OpenSkyHawk/OpenSkyhawk/docs/hardware/cad-workflow.md

---
status: stub
---

# CAD Workflow

!!! warning "Work in Progress"
    This page is being written. Check back soon or
    [contribute to the docs](../contributing/index.md).

!!! note "CAD Tooling Under Evaluation"
    CAD tooling is currently being evaluated between Fusion 360 and FreeCAD.
    FreeCAD is the preferred direction for alignment with the open source nature
    of the project. This page will be updated once a tool is selected.
    The file management policy (source files committed, STL/STEP exports
    gitignored and published via GitHub Releases) applies regardless of tool choice.
