OpenSkyHawk/OpenSkyhawk/Firmware/ScratchPad/TechSpec/STM32Board.md

# STM32Board — Technical Specification

**Status:** Done

**FirmwarePlan ref:** `FirmwarePlan/08-hardware-firmware-contracts.md#status-led--bi-color-redgreen`,
`FirmwarePlan/08-hardware-firmware-contracts.md#diagserial--usart1`,
`FirmwarePlan/02-can-protocol.md#can-bus-configuration`,
`FirmwarePlan/09-startup-resync-diagnostics.md`

**Depends on:** `CANProtocol.md` (for the `CanStatus` event type)

---

## Responsibility

Initialises and manages all shared hardware present on every STM32 board: SWD-only debug (JTAG
released at boot, #299), bi-color status LED (PB14/PB15), DiagSerial (USART1/Serial1), and CAN
peripheral hardware configuration. Exposes
`NODE_ID` (compile-time constant from build_flags) with range validation at compile time.
Owns the LED state machine and tick-based animation driver.

Reacts to CAN bus status events via `onCanStatus()` — it does not poll CANProtocol and is
not directly controlled by the sketch or by CANProtocol. `CanStatus` is owned by
CANProtocol; STM32Board only translates those events into its private LED state machine.

Does **not** start the CAN peripheral or configure receive filters — that belongs to
`CANProtocol::start()`. Does not own any panel-specific I/O.

---

## File Layout

```
Firmware/Libraries/STM32Board/
├── STM32Board.h
├── STM32Board.cpp
└── library.json
```

Included in every STM32 sketch:
```cpp
#include <STM32Board.h>
```

Implemented as a `namespace` — there is always exactly one STM32 board per firmware build,
so a class with instances would be a fiction. Internal state variables are defined in
`STM32Board.cpp` only (not exposed in the header), keeping the public API clean.

### Test project

```
Firmware/Tests/STM32Board/
├── platformio.ini                 — 3 visual envs + 4 STM32BOARD_TEST assertion envs
│                                    + 2 ADC-prescaler envs
└── tests/
    ├── led_state_machine/
    │   └── led_state_machine.cpp   — visual: cycles all 7 LedStates (onCanStatus 4 + setLinkActive
    │                                 CONNECTED + setWarning WARNING); OFF shown pre-begin()
    ├── diag_serial/
    │   └── diag_serial.cpp         — setDebug(false): log() produces no output; setDebug(true):
    │                                 log() emits the expected string on Serial1 at 115200 baud
    ├── can_status_wiring/
    │   └── can_status_wiring.cpp   — calls onCanStatus() with each CanStatus value; verifies
    │                                 the correct LedState is entered (checks pin behaviour via tick())
    ├── state_precedence/           — [STM32BOARD_TEST] currentState() asserts the precedence table:
    │                                 CONNECTED engage/suppress/re-engage, WARNING vs CAN faults
    ├── link_decay/                 — [STM32BOARD_TEST] CONNECTED → NORMAL after LINK_DECAY_MS;
    │                                 refresh holds it
    ├── warning_clear/              — [STM32BOARD_TEST] setWarning(true/false) latch; no-arg raises
    ├── animation_timing/           — [STM32BOARD_TEST] CONNECTED solid (no toggle) vs NORMAL blink,
    │                                 via direct PB14/PB15 pin reads
    ├── jtag_release/
    │   └── jtag_release.cpp        — PA15/PB4 as input + pull-down via HAL_GPIO_Init (not pinMode,
    │                                 which releases them itself): read 1 before begin() (JTAG's
    │                                 pull-up wins), 0 after (GPIO owns them). #299
    └── adc_clock/
        └── adc_clock.cpp           — asserts ADCPRE == /6 and ADCCLK inside the F103 window (#263).
                                      Built into TWO envs: test_adc_clock (72 MHz path) and
                                      test_adc_clock_fallback (-DFORCE_CLOCK_FALLBACK, 8 MHz path)
                                      — the pair is what proves both SystemClock_Config exit paths
                                      set it. Also prints liveTemp/liveVdd for before/after.
```

The four `STM32BOARD_TEST` envs, the two `adc_clock` envs and `jtag_release` print `PASS`/`FAIL` per assertion plus
an `ALL PASS` summary over DiagSerial; the three visual envs are observed against the animation map.

> **Status-LED convention in this suite.** No sketch here calls `CANProtocol::start()` — they test
> `STM32Board` in isolation — so `_canStatus` never leaves its initial `CanStatus::STARTING` and
> `_recompute()` parks in **`BOOTING` (red 1 s blink) for the whole run**. That resting state is
> indistinguishable from a node that failed to bring CAN up, and it says nothing about whether the
> assertions passed.
>
> `adc_clock` therefore drives the LED from its **result**: pass → `onCanStatus(CanStatus::NORMAL)`
> → **green 1 Hz**, the healthy-node pattern; fail → `setWarning(true)` → red/green alternating. A
> **red 1 s blink means `setup()` never reached the end.** `onCanStatus()` is a result indicator
> here, not a claim about the bus (`led_state_machine` drives it artificially too, and neither
> sketch starts CAN). In `test_adc_clock_fallback` the faked dead crystal latches `_clockFault`,
> which outranks both, so that env always shows WARNING — read it by DiagSerial.
>
> Separately, halting the core under SWD (`dump_image`, `mdw`, a paused upload) freezes the GPIOs
> mid-blink; caught on an LED-on phase it sits **solid**, resembling `BUS_OFF` (solid red) or
> `CONNECTED` (solid green) when the CPU is merely stopped.

`adc_clock` asserts the `ADCPRE` bits in both envs — those are what the change writes, and they are
exact. The frequency is pinned to a literal only on the 72 MHz path, where `72e6 / 6 = 12000000`
exactly; the fallback's `8e6 / 6` truncates to 1333333, so there it is printed and range-checked
against the 0.6–14 MHz window instead of hard-coded.

`can_status_wiring.cpp` verifies the mapping from CANProtocol's `CanStatus` values to
STM32Board's private LED states, so both libraries must be in `lib_deps`:

```ini
[platformio]
src_dir = tests

[env_base]
platform = ststm32@^20.0.0
board = genericSTM32F103C8
framework = arduino
build_flags =
    -DNODE_ID=1
    -DHAL_CAN_MODULE_ENABLED
    -DUSB_NONE
    -DHSE_VALUE=8000000
lib_extra_dirs = ${PROJECT_DIR}/../../Libraries
lib_deps =
    STM32Board
    CANProtocol

[env:test_led_state_machine]
extends = env_base
build_src_filter = -<*> +<led_state_machine/led_state_machine.cpp>

[env:test_diag_serial]
extends = env_base
build_src_filter = -<*> +<diag_serial/diag_serial.cpp>

[env:test_can_status_wiring]
extends = env_base
build_src_filter = -<*> +<can_status_wiring/can_status_wiring.cpp>

; Same source, two envs — the second forces the SystemClock_Config fault path (#263)
[env:test_adc_clock]
extends = env_base
build_src_filter = -<*> +<adc_clock/adc_clock.cpp>

[env:test_adc_clock_fallback]
extends = env_base
build_flags = ${env_base.build_flags} -DFORCE_CLOCK_FALLBACK
build_src_filter = -<*> +<adc_clock/adc_clock.cpp>
```

CAN bus integration testing is out of scope here — see CANProtocol TechSpec.

---

## Public API

```cpp
// STM32Board.h

enum class CanStatus;

namespace STM32Board {

    /**
     * @brief Initialise all shared hardware. Call once at the top of setup().
     *
     * Releases JTAG and keeps SWD (#299), so PA15 / PB3 / PB4 are ordinary GPIO from here on.
     * Configures PB14 (Red) and PB15 (Green) as outputs and enters BOOTING state.
     * Starts DiagSerial (USART1, PA9/PA10, 115200 baud) — silent until setDebug(true).
     * Calls analogReadResolution(16) — framework scales 12-bit ADC output to 16-bit range
     * (0–65520) for all subsequent analogRead() calls; PinRef::readAnalog() relies on this.
     * The ADC clock itself is set earlier, in SystemClock_Config (ADCPRE /6 → 12 MHz, #263) —
     * begin() only reads it back for the diag line.
     * Configures the CAN peripheral at 500 kbps on PA11/PA12 but does NOT start it —
     * call CANProtocol::start() after filter setup.
     * NODE_ID range (0–63) is validated at compile time via static_assert.
     */
    void begin();

    /**
     * @brief Enable or disable DiagSerial output.
     *
     * DiagSerial is always initialised by begin(); this flag gates all log() calls.
     *
     * @param on True to emit output on USART1; false for silence (default).
     */
    void setDebug(bool on);

    /**
     * @brief Drive LED animations. Call once per loop() iteration.
     *
     * Advances blink state using millis(). Fully non-blocking — no busy-wait or delay.
     */
    void tick();

    /**
     * @brief CAN bus status event handler.
     *
     * Called when CANProtocol fires a status change.
     * Maps CanStatus to an internal LedState — the sketch and CANProtocol never
     * access the LED directly.
     *
     * @param status New CAN bus status reported by CANProtocol.
     * @note CanStatus is defined by CANProtocol.h and forward-declared here to keep
     *       STM32Board.h light. STM32Board.cpp includes CANProtocol.h for the enum values.
     */
    void onCanStatus(CanStatus status);

    /**
     * @brief Raise or clear the WARNING condition — red/green alternating at 500 ms.
     *
     * Call for any non-CAN fault: dead PanelGroup node (PanelBridge), lost master
     * heartbeat (PanelGroup), SYNC timeout, I²C bus hang. CanStatus has no WARNING value —
     * this is the only public entry point for that state. WARNING is a clearable latch:
     * call setWarning(false) once the condition recovers. It outranks CONNECTED/NORMAL but
     * is masked by any CAN fault (CAN_ERROR/BUS_OFF).
     *
     * @param on True to raise WARNING (default); false to clear it.
     */
    void setWarning(bool on = true);

    /**
     * @brief Signal that application data is flowing → CONNECTED (green solid).
     *
     * Call setLinkActive(true) on each unit of inbound data (PanelBridge: a DCS-BIOS export
     * seen; PanelGroup: a CTRL_BCAST received). The link auto-decays back to NORMAL after
     * ~500 ms (LINK_DECAY_MS) with no further calls, evaluated inside tick(). CONNECTED is
     * shown only while the CAN bus is healthy; a CAN fault masks it and it re-engages
     * automatically on recovery if data is still flowing.
     *
     * @param active True to (re)assert the data-flowing link; false to drop it immediately.
     */
    void setLinkActive(bool active);

    /**
     * @brief Returns true when debug output is enabled.
     *
     * Guard multi-field formatted print blocks with this to avoid string formatting
     * overhead when debug is off.
     */
    bool isDebug();

    /**
     * @brief Print a line to DiagSerial if debug is enabled; no-op otherwise.
     * @param msg Null-terminated string to print.
     */
    void log(const char* msg);

    /**
     * @brief Access DiagSerial directly for multi-field formatted output.
     *
     * Guard with isDebug() to avoid formatting overhead when debug is off.
     *
     * @returns Reference to the USART1 Uart instance.
     */
    Uart& diagSerial();

    /**
     * @brief Read the MCU internal die temperature (ADC ch16) as whole °C (#213).
     *
     * Reads ATEMP + AVREF (Vrefint) and converts with F103 datasheet typicals
     * (V25 = 1.43 V, Avg_Slope = 4.3 mV/°C), referencing Vsense to the measured Vdd.
     * UNCALIBRATED — ~±few °C absolute, die (not ambient), self-heat offset.
     *
     * @returns Die temperature in whole °C, or INT8_MIN if internal channels are unavailable.
     */
    int8_t readDieTempC();

    /**
     * @brief Estimate MCU Vdd from Vrefint (ADC ch17), in millivolts (#213).
     *
     * @note Uses the F103 typical Vrefint of 1.20 V (no VREFINT_CAL on F103).
     * @returns Vdd in millivolts, or 0 if the internal reference is unavailable.
     */
    uint16_t readVddMv();

    /**
     * @brief Edge-log a node's aggregated fault transition to DiagSerial (#163).
     *
     * Prints `[<tag>] degraded: <detail> (fault N)` / `[<tag>] recovered` on a change only,
     * isDebug()-gated. Shared by every node's health-TX loop (PanelGroup "NODE", PanelBridge
     * "BRIDGE", future PDU) — one static prev-fault, correct because a binary has ONE node
     * identity. Detail strings stay local (never on the CAN wire).
     */
    void logNodeFaultEdge(const char* tag, NodeFaultCode fault, const char* detail);

    static constexpr uint8_t PIN_LED_RED   = PB14;  ///< Red LED pin — same on all STM32 boards
    static constexpr uint8_t PIN_LED_GREEN = PB15;  ///< Green LED pin — same on all STM32 boards

} // namespace STM32Board
```

NODE_ID compile-time validation, placed at file scope in `STM32Board.h`:
```cpp
static_assert(NODE_ID <= 63,
    "NODE_ID must be 0–63. 0 = PanelBridge (reserved); 1–63 = PanelGroup nodes.");
```

### Sketch wiring

The sketch is the integration point:

```cpp
// setup()
STM32Board::begin();
CANProtocol::onStatusChange(STM32Board::onCanStatus);
CANProtocol::start();

// loop()
STM32Board::tick();
```

`CANProtocol::onStatusChange()` is defined in the CANProtocol TechSpec.

---

## Key Data Structures

### LedState (private enum)

```cpp
enum class LedState {
    OFF,        // both LEDs off — pre-begin() only
    BOOTING,    // red slow blink  (1000 ms) — initialising
    NORMAL,     // green slow blink (1000 ms) — CAN healthy, no data flowing
    CONNECTED,  // green solid                — CAN healthy and data flowing
    CAN_ERROR,  // red fast blink  (250 ms)  — TEC > 0, errors accumulating
    BUS_OFF,    // red solid                  — CAN controller halted
    WARNING     // red/green alternating (500 ms) — app-layer degraded state
};
```

`LedState` is an internal type — not exposed in the public API. The on-target tests need to
assert it, so the `STM32BOARD_TEST` macro (set only by the test envs) moves the enum to the
header and exposes a read-only `LedState currentState()` accessor; production builds keep both
private.

### LedState → Animation Map

| State | Red | Green | Blink period |
|---|-----|---|---|
| `OFF` | off | off | — |
| `BOOTING` | blink | off | 1000 ms |
| `NORMAL` | off | blink | 1000 ms |
| `CONNECTED` | off | solid on | — |
| `CAN_ERROR` | blink | off | 250 ms |
| `BUS_OFF` | solid on | off | — |
| `WARNING` | alternating | alternating | 500 ms |

For `WARNING`: phase 0 → red on, green off; phase 1 → red off, green on.

### State arbitration & precedence

The LED state is **derived**, not set last-writer-wins. `STM32Board` stores three independent
inputs — the last `CanStatus`, a data-flowing link flag (with timestamp, set by
`setLinkActive`), and a warning latch (`setWarning`) — and a single internal `_recompute()`
picks the effective `LedState` by fixed precedence (highest first):

| Priority | Condition | LedState |
|---|---|---|
| 1 | not begun | `OFF` |
| 2 | `CanStatus::BUS_OFF` | `BUS_OFF` |
| 3 | `CanStatus::TX_ERROR` | `CAN_ERROR` |
| 4 | `CanStatus::STARTING` | `BOOTING` |
| 5 | warning latched | `WARNING` |
| 6 | `CanStatus::NORMAL` **and** link active | `CONNECTED` |
| 7 | `CanStatus::NORMAL` | `NORMAL` |

CAN-health faults outrank the app-layer WARNING (a dead/erroring bus must never be masked).
WARNING outranks CONNECTED/NORMAL. CONNECTED is guarded on `NORMAL`, so a CAN fault
auto-suppresses it and it re-engages on recovery if the link has not yet decayed
(`LINK_DECAY_MS` = 500 ms). `_recompute()` resets the blink phase and repaints only on an
actual state change.

### CanStatus → LedState mapping

`onCanStatus()` stores the `CanStatus` and calls `_recompute()`; rows 2–4, 6–7 above are the
effective mapping (CONNECTED/NORMAL both correspond to `CanStatus::NORMAL`, differentiated by
the link flag):

| CanStatus | LedState (no link) | LedState (link active) |
|---|---|---|
| `STARTING` | `BOOTING` | `BOOTING` |
| `NORMAL` | `NORMAL` | `CONNECTED` |
| `TX_ERROR` | `CAN_ERROR` | `CAN_ERROR` |
| `BUS_OFF` | `BUS_OFF` | `BUS_OFF` |

`CanStatus` is defined in `CANProtocol.h`. See CANProtocol TechSpec for the full enum.

> **ERROR_PASSIVE (EPVF / TEC ≥ 128)** is intentionally **not** a distinct LED state — it stays
> folded into `CAN_ERROR`, and EPVF remains visible via the heartbeat `flags` byte. See
> `FirmwarePlan/11-open-issues.md` (re-confirmed in #93).

---

## Implementation Notes

### tick() — blink state machine

```cpp
void STM32Board::tick() {
    uint32_t now = millis();

    // Decay the data-flowing link → CONNECTED falls back to NORMAL after a quiet gap.
    if (_linkActive && (now - _linkLastMs) >= LINK_DECAY_MS) {
        _linkActive = false;
        _recompute();
    }

    uint16_t period = _blinkPeriodFor(_state);  // 0 = solid or off
    if (period > 0 && (now - _ledLastToggleMs) >= (uint32_t)(period / 2)) {
        _blinkPhase      = !_blinkPhase;
        _ledLastToggleMs = now;
        _applyLed();  // only called when phase actually changes
    }
    // solid/off states: pins already set by _recompute() — nothing to do here
}
```

`_applyLed()` is called in two places only:
- Inside `_recompute()` — applies the new state immediately on a transition (and only then)
- Inside `tick()` — only when `_blinkPhase` toggles

`_recompute()` is the **sole writer** of `_state`: `onCanStatus()`, `setWarning()`,
`setLinkActive()`, and the `tick()` decay path all update one input field and call it.

`digitalWrite()` is called exactly twice per blink cycle for blinking states, and once per
state transition for solid and off states. Pins are never written redundantly.

### NODE_ID — PanelBridge reservation

`NODE_ID=0` is reserved for PanelBridge. PanelBridge is a STM32 board and a valid CAN bus
participant, but it is the master node — it does not have a sub-node address in the
0x101–0x43F frame ID ranges used by PanelGroup nodes.

The `static_assert` uses `<= 63` (no lower bound) so PanelBridge passes with `NODE_ID=0`:

```cpp
static_assert(NODE_ID <= 63,
    "NODE_ID must be 0–63. 0 is reserved for PanelBridge; 1–63 for PanelGroup nodes.");
```

SimGateway is an RP2040 — it does not use STM32Board and has no NODE_ID concern.

### CAN peripheral configuration

`begin()` configures the STM32 CAN peripheral (baud rate prescaler, segment timing for
500 kbps, PA11/PA12 alternate function) but does **not** call the HAL start function.
The peripheral is left configured-but-stopped — ready for `CANProtocol::start()`.

**Library choice:** direct STM32duino HAL (`CAN_HandleTypeDef`, `HAL_CAN_Init`) — no
wrapper library. Confirmed by the prototype CAN stress test (Experiment B).

**Clock tree:** 8 MHz crystal × PLL ×9 = 72 MHz SYSCLK; APB1 prescaler /2 = **36 MHz APB1**
(STM32F103 APB1 max is 36 MHz; CAN1 is on APB1); APB2 prescaler /1 = **72 MHz APB2**, from which
`ADCPRE` /6 gives **12 MHz ADCCLK** — see *ADC clock configuration* below.

**Clock selection is not automatic (issue #245).** The `genericSTM32F103C8/CB` core ships a
`__weak SystemClock_Config` that defaults SYSCLK to **HSI-PLL 64 MHz** — APB1 would be 32 MHz and
the CAN init struct below would produce **444 kbps, not 500**. `-DHSE_VALUE=8000000` only tells HAL
the crystal frequency; it does *not* select HSE. `STM32Board` therefore provides a **strong**
`SystemClock_Config` that selects HSE → PLL ×9 → 72 MHz. Every STM32 node links `STM32Board`, so
the whole fleet inherits it in one place (PanelBridge included).

After configuring, it **reads back** `HAL_RCC_GetSysClockFreq()`/`GetPCLK1Freq()` and requires
exactly 72/36 MHz. This catches **HSE-start failure** (dead crystal / cold joint → HSERDY timeout →
`HAL_RCC_OscConfig` errors) and a self-inconsistent config, but **not a wrong-value crystal**: those
freqs are computed from the RCC config × the compile-time `HSE_VALUE`, not measured, so a 12 MHz part
computes (and passes) as 72 MHz while really running 108 MHz. Correct crystal value is a BOM/build
guarantee, not runtime-detectable without an independent reference (LSE/LSI cross-count), which we do
not implement. On a detected deviation it latches `_clockFault` and falls back to internal RC; `begin()`
then drives the **WARNING** LED (alternating), which is given **top precedence in `_recompute`**
so a clock fault is not masked by the CAN TX errors it induces (which would misread as a bus fault).
`begin()` also logs `CLOCK OK/FAULT: SYSCLK=.. PCLK1=.. CAN=..bps ADC=..kHz` on the diag UART
(ADCCLK in **kHz**, not MHz, so the fault path's 1.33 MHz does not render as a misleading `1MHz`).
Nothing parses this line — it is diagnostic output, not a contract. The fault path is bench-testable
via `-DFORCE_CLOCK_FALLBACK` without disturbing the crystal.

**Confirmed HAL init struct** — validated in Experiment B (21-min soak, 1,257 frames, 0 lost, TEC=0):

```cpp
_hcan.Instance               = CAN1;
_hcan.Init.Prescaler         = 4;              // 36 MHz APB1 / 4 / 18TQ = 500 kbps
_hcan.Init.Mode              = CAN_MODE_NORMAL;
_hcan.Init.SyncJumpWidth     = CAN_SJW_4TQ;   // must be 4TQ — Blue Pill clone tolerance
_hcan.Init.TimeSeg1          = CAN_BS1_13TQ;
_hcan.Init.TimeSeg2          = CAN_BS2_4TQ;   // total: 1+13+4 = 18TQ
_hcan.Init.TimeTriggeredMode = DISABLE;
_hcan.Init.AutoBusOff        = ENABLE;         // hardware recovery ~3 ms, no firmware action needed
_hcan.Init.AutoWakeUp        = DISABLE;
_hcan.Init.AutoRetransmission = DISABLE;       // prevent runaway bus-off — see CANProtocol HAL notes
_hcan.Init.ReceiveFifoLocked  = DISABLE;       // overwrite oldest on FIFO full (consistent with drop-oldest policy)
_hcan.Init.TransmitFifoPriority = DISABLE;     // TX priority by message ID (standard CAN arbitration)
```

> **Note:** the comment `72 MHz / 4 / (1+13+4) = 500 kbps` in the source is a simplification.
> The actual CAN clock is APB1 = 36 MHz. The HAL uses the real APB1 clock at init time, so the
> parameters produce 500 kbps — **but only because `SystemClock_Config` guarantees 72 MHz SYSCLK.**
> Without that (core default HSI 64 MHz → APB1 32 MHz) the same struct yields 444 kbps. See #245.

**Scope boundary:** STM32Board's responsibility ends at configuring the peripheral.
Verifying that the bus comes up at 500 kbps and that frames flow correctly is out of scope
here — that belongs to the CANProtocol breadboard test.

### ADC clock configuration (#263)

`SystemClock_Config` also owns `ADCPRE`, via a file-static `_configAdcClock()` helper:

```cpp
static void _configAdcClock(void) {
    RCC_PeriphCLKInitTypeDef adc = {};
    adc.PeriphClockSelection = RCC_PERIPHCLK_ADC;
    adc.AdcClockSelection    = RCC_ADCPCLK2_DIV6;
    (void)HAL_RCCEx_PeriphCLKConfig(&adc);   // F1 ADC branch cannot fail; cast is deliberate
}
```

**Why `STM32Board` owns it.** On F1 the STM32duino core declines to set the ADC prescaler —
`analog.cpp` guards its `__HAL_RCC_ADC_CONFIG` with `!defined(STM32F1xx)` and defers to
`SystemClock_Config` — and `variant_generic.cpp`, the variant our strong override displaces, never
set it either. So `ADCPRE` sat at its reset `/2` and ADCCLK booted at **36 MHz against the F103's
14 MHz maximum**. `/4` = 18 MHz is still out of spec, so `/6` → **12 MHz** is the fastest legal
divider. HAL rather than a raw `RCC->CFGR` write, matching `variant_PILL_F103Cx.cpp` (which sets the
same value) and the rest of this file; its `RCC_PERIPHCLK_USB` branch is omitted deliberately —
every OpenSkyhawk STM32 env builds `-DUSB_NONE`.

**Both exit paths.** `SystemClock_Config` returns early once the 72 MHz tree verifies, and falls
through to an HSI-8 MHz fault path otherwise. `_configAdcClock()` is called on **both** — a single
write at the early `return` would leave `ADCPRE` at reset on every faulted board. On the fault path
8 MHz / 6 = 1.33 MHz, still above the F103's 0.6 MHz minimum.

**Ordering.** The core calls `SystemClock_Config` from `hw_config_init()` *before* `setup()`, so the
framework's own lazy ADC init inside the first `analogRead()` inherits the prescaler. No call
ordering is required of the sketch.

**Cost.** Conversions take 3× longer: 13.5 sample + 12.5 convert = 26 cycles, 0.72 µs → 2.17 µs.
`analogRead()` measures ~56.5 µs end-to-end at 36 MHz and ~63 µs at 12 MHz (its per-call 83-cycle
calibration triples too). Irrelevant against `AnalogInput::POLL_MS` = 8 ms. `ADCPRE` divides PCLK2
to feed only the ADCs, so CAN, the UARTs, SPI/ShiftBus and the timers are unaffected.

> **This fixed nothing observable.** Axis noise, PA2, and die-temperature telemetry were each
> predicted to improve and each measured *unchanged* on the assembled PanelGroup Rev 1. The
> justification is that the part was out of spec, plus high-impedance sources in general — which has
> **not** been measured on an actual potentiometer. See `FirmwarePlan/00-decisions.md` D15 for the
> measurements and the rigs that could settle the pot question.

### JTAG release (#299)

Every OpenSkyhawk STM32 board is SWD-only (`J_SWD`: SWDIO / SWCLK / NRST), but the F103 boots
with full SWJ, so PA15 (JTDI), PB3 (JTDO) and PB4 (NJTRST) start as JTAG pins. The first thing
`begin()` does is `__HAL_RCC_AFIO_CLK_ENABLE(); __HAL_AFIO_REMAP_SWJ_NOJTAG();`: JTAG off,
SWD (PA13/PA14) kept, so ST-Link still flashes and debugs, and the three pins are ordinary GPIO
for whatever class touches them.

- **Order-independent.** Later HAL remaps (`AFIO_REMAP_ENABLE`, used for the I2C1 / SPI1
  remaps) write `SWJ_CFG = 0b111`, which RM0008 defines as "no effect". They can't undo it, and
  the SWJ bits being write-only doesn't matter.
- **Redundant elsewhere, kept.** The core frees these pins per-pin in `pinMode()` /
  `attachInterrupt()` (`pinF1_DisconnectDebug`, unless `STM32F1_LOCK_DEBUG`), and
  `ShiftBus::begin()` does it for PB3/PB4. Both still run and are harmless; `begin()` makes it
  board policy rather than a side effect of which class touches a pin first.
- **Verified on hardware (2026-09-21):** `jtag_release` passes. With the two lines commented out
  it fails (PA15 / PB4 still read 1 after `begin()`), so the test can fail. SWD attaches to and
  halts the running firmware without a reset.

### DiagSerial — always initialised, gated by flag

`Serial1.begin(115200)` is called unconditionally in `begin()` so the pins (PA9/PA10) are
always claimed. All `diagPrint*` calls check `_debugEnabled` and return immediately if false.
No `#ifdef DEBUG` guards — zero runtime cost when disabled.

---

## Dependencies

| Dependency | Source | Notes |
|---|---|---|
| STM32duino Arduino core | PlatformIO `framework = arduino` | `millis()`, `pinMode()`, `digitalWrite()`, `Serial1` |
| STM32duino HAL CAN | STM32duino Arduino core | Direct `CAN_HandleTypeDef` / `HAL_CAN_Init` — no wrapper library needed |
| `CanStatus` enum | `CANProtocol.h` | Owned by CANProtocol; forward-declared in `STM32Board.h`, included by `STM32Board.cpp` for value mapping |
| `NodeFaultCode` enum | `NodeStatus.h` | Included by `STM32Board.h` for the `logNodeFaultEdge()` signature (#163); NodeStatus is a leaf lib |
| `NODE_ID` define | `platformio.ini` `build_flags` | Must be present; compile fails otherwise |
