OpenSkyHawk/OpenSkyhawk/tools/docs-drift/REVIEW.md

# Weekly Docs Drift Review — Playbook

This is the procedure the **`weekly-docs-drift-review`** scheduled task follows. It is run
by a fresh Claude with no memory of prior runs, so everything needed is here. The job is to
catch *prose* drift that structured checks can't: new hardware that has no page, and design
decisions that changed in a source file but not on the published page.

Structured tables (NODE_IDs, etc.) are already kept in sync by transclusion +
`tools/check_node_ids.py` — **do not** re-check those here.

**Line-number citations are machine-checked too.** `tools/docs-drift/check_doc_refs.py` runs
in CI on every PR touching `docs/**` or `Firmware/**` and asserts that each `` `File.h:N` ``
on a published page still resolves *and* — in a table row that names an identifier — still
lands on a line containing it. Don't spend review time re-verifying those by hand; if the
check is green, they hold. What it deliberately does **not** cover, and you still should:
a documented diagnostic string transcribed into prose (field names, units, ordering), which
has no citation to anchor it.

## Ground rules

- **Read-only on tracked content.** This run opens or updates one GitHub issue. It does
  **not** edit docs, commit, or push. Its only local write is the scratch file
  `docs-drift-body.tmp` in the repo root, which `.gitignore` already covers via `*.tmp`.
- **Nothing is checked out.** Every command below reads `origin/main` straight out of the
  object database (`git log`/`git grep`/`git show <rev>:<path>`). No worktree, no branch
  switch, no index write — the user's working tree and uncommitted changes are untouchable
  by construction. The scheduled-task prompt only does `git fetch origin main`.
- **Assume cwd is the repo root** and stay there. Every shell command must be a **single
  `git` or `gh` invocation** — no `cd`, no pipes, no subshells, no `$(...)`, no `$'...'`. The
  scheduled task runs non-interactively, so a command that misses the permission allow-list
  stops the run dead waiting for an approval nobody is there to give; compound commands and
  exotic quoting are what miss. The one non-`git`/`gh` tool call in the whole run is the
  **Write** of the issue body to `docs-drift-body.tmp` (Step 5).
- **Ignore `docs/api/**`** — those pages are generated by mkdoxy; they are never drift.
- Output is a single issue labelled `docs-drift`. Re-running updates the same open issue
  rather than spawning duplicates.

## Source of truth → published docs

| Source of truth (what changed) | Published surface (what to keep in sync) |
|---|---|
| `docs/_source/**` (architecture, `hardware-standards.md`, `pcb-design-rules.md`, `kicad.md`, `controllers/`) | `docs/**` prose pages (excluding `docs/api/`, `docs/_source/`) |
| `CLAUDE.md` (project rules, decisions) | architecture / contributing / hardware pages |
| `Firmware/Panels/**`, `Firmware/Libraries/**`, `Firmware/NODE_IDS.md` | `docs/firmware/**`, panel pages |
| `PCB/**`, `CAD/**` (new boards / panels) | `docs/hardware/**`, `docs/panels/**`, kit pages |
| **GitHub Projects #2** (Controller Build, org `OpenSkyHawk`) — panel/controller past the schematic stage (B2+) | a matching page must exist under `docs/` |

## Step 1 — Establish the window

```bash
git log origin/main --since="7 days ago" --pretty='%h %ad %s' --date=short
```

If there are **no** commits in the window, post the "no drift" note (Step 5) and stop.

## Step 2 — Gather source-of-truth changes

```bash
git log origin/main --since="7 days ago" --name-only --pretty='%n=== %h %s' -- \
  docs/_source CLAUDE.md \
  Firmware/Libraries Firmware/Panels Firmware/NODE_IDS.md \
  PCB CAD
```

Read the actual diffs for anything that looks like a decision or a new component:

```bash
git log origin/main --since="7 days ago" -p -- docs/_source/hardware-standards.md CLAUDE.md \
  docs/_source/architecture.md docs/_source/pcb-design-rules.md
```

Also list directories that are **new** in the window (candidate new hardware with no page):

```bash
git log origin/main --since="7 days ago" --diff-filter=A --name-only --pretty=format: -- \
  PCB CAD Firmware/Panels
```

(Expect repeats across commits — dedupe by eye rather than piping to `sort -u`; a pipe
introduces a second command that the allow-list does not cover.)

## Step 3 — Compare against the published docs

For each changed source item, decide whether a published page is now wrong or missing.

- **New hardware → missing page.** A new `PCB/<Console>/<Group>/<Board>/`, new
  `CAD/<...>`, or new `Firmware/Panels/<Panel>/` should have a corresponding page under
  `docs/hardware/`, `docs/panels/`, or a kit page. Grep the docs for the board/panel name:
  ```bash
  git grep -il "<Board or Panel name>" origin/main -- 'docs/**.md' \
    ':(exclude)docs/api' ':(exclude)docs/_source'
  ```
  No hit → flag as **missing page**.
- **Changed decision → stale page.** When a value or decision changed in a source file
  (e.g. a part number in `hardware-standards.md`, an MCU-variant rule, a design decision
  D1–D8 such as the CAD tool choice), grep the published pages for the **old** value and
  confirm none still assert it:
  ```bash
  git grep -in "<old value / old decision>" origin/main -- 'docs/**.md' \
    ':(exclude)docs/api' ':(exclude)docs/_source'
  ```
  Any hit on a published page → flag as **stale decision**.
- **Contradiction.** If a published page states something that now conflicts with
  `docs/_source/` material, flag it with both locations.

To read a full page (or any source file) at `origin/main` without checking it out:

```bash
git show origin/main:docs/<section>/<page>.md
```

Use judgement — only flag real, actionable mismatches. A reworded sentence in a source
file with no factual change is **not** drift.

## Step 4 — Build-page cross-check (best effort)

Panel and controller **build tracking lives in GitHub Projects** (org `OpenSkyHawk`), **not
Notion** — the legacy Notion Panels DB is research-reference only, so do **not** use it as
the build tracker. If GitHub Projects is reachable, list **Project #2 (Controller Build)**
items and confirm each controller/panel past the schematic stage (B2+) has a page under
`docs/`:

```bash
gh project item-list 2 --owner OpenSkyHawk --format json
```

Flag any built/in-progress controller or panel with no docs page. If the check can't run,
note "build-page cross-check skipped" in the issue and continue — do not fail. (Notion still
holds non-panel data — Tasks DB, project notes — but that is out of scope for this review.)

## Step 5 — Write the issue

Ensure the label exists (no-op if it already does):

```bash
gh label create docs-drift --color FBCA04 --description "Docs site has drifted from a source of truth"
```

It errors harmlessly if the label already exists; don't wrap it in `|| true` — the `||`
splits it into two commands and costs a permission prompt.

Find an existing open issue and reuse it:

```bash
gh issue list --label docs-drift --state open --json number,title
```

- **Findings exist:** write the markdown body (template below) to `docs-drift-body.tmp` in
  the repo root with the **Write tool**, then pass it with `--body-file` — never inline via
  `--body` (see *Passing the body* below). If an open `docs-drift` issue exists,
  `gh issue edit <n> --body-file docs-drift-body.tmp` and add a dated comment noting the
  refresh; otherwise
  `gh issue create --label docs-drift --title "Weekly docs drift review — <YYYY-MM-DD>" --body-file docs-drift-body.tmp`.
- **No findings:** if an open issue exists, comment "No new drift detected as of `<date>`.";
  if none exists, do nothing (don't open an empty issue).

### Issue body template

```markdown
# Docs drift — week ending <YYYY-MM-DD>

Reviewed source-of-truth changes from the last 7 days against the published docs.
Ignored `docs/api/` (auto-generated).

## 🆕 New hardware without a page
- [ ] `<source path>` (added <short-sha>) — no page found under `docs/`. Suggest: `docs/<section>/<page>.md`.

## ♻️ Stale decisions
- [ ] `<doc page>` still says "<old>"; `<source file>` changed it to "<new>" (<short-sha>).

## ⚠️ Contradictions
- [ ] `<doc page>` conflicts with `<source file>`: <one line>.

## Notes
- Build-page cross-check (GitHub Projects #2): <done / skipped>.
- Commits reviewed: <range or shas>.
```

### Passing the body

**Never put the markdown body on a shell command line.** Both ways of quoting it are held for
approval, which stalls an unattended run at the last step with all the work already done:

| Form | What the checker says |
|---|---|
| `--body "…<newline>## Heading…"` | *Newline followed by # inside a quoted argument can hide arguments from path validation* |
| `--body $'…\n## Heading…'` | *Contains ansi_c_string* |

Both were observed on live runs (2026-09-20). Write the body to a file instead, so its text
never passes through shell quoting at all:

1. **Write tool** → `docs-drift-body.tmp`, in the **repo root**.
2. `gh issue create --label docs-drift --title "…" --body-file docs-drift-body.tmp`

The path matters. A file under `/tmp` is refused with *"Path is outside allowed working
directories"* — a third check, independent of the allow-list, which a `Write(/tmp/...)` rule
does **not** satisfy. Keeping the file inside the workspace is what avoids it; `*.tmp` is
already in `.gitignore`, so the scratch file can never be committed.

This is the one deliberate exception to "no temp files" — it buys a body that is never
shell-quoted. Nothing reads the file afterwards; leaving it in place is fine.

Keep each item to one actionable line that cites the source commit/file and the target
page. Group empty sections may be omitted.

## Maintaining this playbook

Improve the review by editing **this file** in a PR — the scheduled task is a thin pointer
to it and does not need to be recreated. Local build/preview steps for verifying any fix
live in [`../../docs/_source/docs-site-workflow.md`](../../docs/_source/docs-site-workflow.md).
