OpenSkyHawk/OpenSkyhawk/Firmware/ScratchPad/FirmwarePlan/00-decisions.md

# 00 — Architecture Decisions

**Owns:** rationale for every non-obvious architectural choice made during design.
**Does not own:** the actual specs — those are in the contract files. This file explains *why*,
not *what*.

Each decision is a one-way door that other files depend on. If a decision changes, every
dependent file must be reviewed.

---

## D1 — SimGateway is a pure byte relay; PanelBridge owns DCS-BIOS

**Decision:** SimGateway forwards raw bytes between USB CDC and UART without parsing them.
PanelBridge runs the DCS-BIOS library.

**Rationale:** STM32 native USB CDC crashes under sustained DCS-BIOS data flow (socat exits
"Permission denied"; port becomes unusable until replug). The RP2040 USB stack handles
250 000 baud DCS-BIOS traffic without issue. Putting the DCS-BIOS library on the RP2040
would complicate SimGateway and split the processing across two devices that communicate
via a single UART — worse latency and harder to debug. PanelBridge on STM32 handles the
DCS-BIOS library cleanly because it never uses USB at runtime.

**Affects:** `01-system-overview.md`, `06-panelbridge-api.md`, `07-simgateway-api.md`.

---

## D2 — controlId routing: 0x8000-0x86FF → DCS-BIOS, < 0x8000 → HID

**Decision:** `controlId` values determine routing path without any additional lookup. Values
in `0x8000`-`0x86FF` are DCS-BIOS compact command IDs routed by PanelBridge; values
`< 0x8000` are HID axes/buttons routed by SimGateway. Values outside both valid routing
spaces, including `0xFFFF`, are reserved/invalid and must not be treated as DCS-BIOS input
commands.

**Rationale:** The A-4E-C mod has no axis exports (stick/rudder are HID-only inputs). The two
ranges therefore never overlap. The DCS-BIOS input range is still bounded so reserved IDs such
as `0xFFFF` cannot accidentally route into the generated input map.

**Affects:** `04-dcs-bios-integration.md`, `06-panelbridge-api.md`, `07-simgateway-api.md`.

---

## D3 — DCSIN_* as compact transport aliases (not device IDs or DCS output addresses)

**Decision:** `DCSIN_*` constants are compact stand-ins for DCS-BIOS command name strings,
required because a CAN frame carries only 8 data bytes — too little for an ASCII command like
`"LIGHT_EXT_MASTER 2\n"`. Multiple input controls may share one `DCSIN_*` constant if they
trigger the same DCS command. PanelBridge does not track which node sent the EVT.

**Rationale:** DCS output addresses identify values *from* DCS to the cockpit. Input controls
send commands *to* DCS. The namespaces are different. Reusing output addresses as input IDs
would conflate two independent concepts. The `DCSIN_*` approach decouples the physical control
from the DCS command it triggers and avoids the 8-byte CAN frame limitation.

**Affects:** `04-dcs-bios-integration.md`, `05-panelgroup-api.md`.

---

## D4 — 16-bit normalisation for all analog inputs (0–65535)

**Decision:** all analog input sources (STM32 ADC, ADS1115, AS5600, MT6701) are normalised to
16-bit before sending over CAN. The 16-bit value is used as-is at the destination — no
rescaling in PanelBridge or SimGateway.

**Rationale:** DCS-BIOS `set_state` controls with `max_value > 1` expect 0–65535 (or integer
strings thereof). Using one resolution throughout eliminates per-destination scaling code and
makes CAN traffic predictable.

The original rationale also cited `Joystick.use16bit()`, from a HID library evaluated before
TinyUSB was selected (D-HID / `03-uart-usb-hid-protocol.md#hid-backend`). That API no longer
exists in the codebase; the decision is unaffected, because 16-bit unsigned remained the right
choice for the reasons above. The backend change moved the conversion rather than the
convention: `HIDAxis::dispatch()` now applies calibration and then `value − 32768`.

The convention has since spread further — axis calibration stores and transmits unsigned
0–65535 for the same reason, and a client carries it unsigned through everything that stores,
compares or sends a value. The conversion stays where it was moved to: `HIDAxis::dispatch()`,
once, on the way into the HID report.

A client may still show the signed view, and a calibration UI should: the number on screen is one
the user will also read in DCS, which shows ±32767. That is a rendering choice at the display
edge, not a change to the convention — the value being committed is unsigned either way.

**Affects:** `05-panelgroup-api.md`, `07-simgateway-api.md`.

---

## D5 — SYNC_REQ / READY handshake for boot ordering and node recovery

**Decision:** PanelBridge broadcasts `SYNC_REQ` (0x012) on cold boot, on DCS session change,
when a PanelGroup sends `READY`, and when a node transitions from dead/unseen to alive. Each
PanelGroup sends a `READY` frame (`0x400+n`) after completing its initial input poll.
PanelGroup also re-polls on any subsequent `SYNC_REQ` it receives.

**Rationale:** PanelGroup nodes may boot before PanelBridge (power sequencing). Without a
handshake, the boot-time input EVT burst is lost and DCS starts with stale switch positions.
The SYNC_REQ mechanism ensures PanelBridge can request a fresh input snapshot at any time —
whether after READY, on cold boot, after a node reconnect, or after a DCS session change.

Missed outputs (LEDs, gauges) are tolerable — a fresh DCS-BIOS update arrives within ~50 ms.
Missed inputs (switch positions) would leave DCS in the wrong state until the next physical
change — this is not tolerable.

**Affects:** `02-can-protocol.md`, `05-panelgroup-api.md`, `06-panelbridge-api.md`,
`09-startup-resync-diagnostics.md`.

---

## D6 — HID frame magic bytes: 0xAA 0x55

**Decision:** HID frames use `0xAA 0x55` as the two-byte header (both bytes have bit 7 set).

**Rationale:** DCS-BIOS ASCII text commands use only printable ASCII + LF (all bytes ≤ 0x7F).
`0xAA` and `0x55` both have bit 7 set, making collision with DCS-BIOS bytes structurally
impossible. No parser state machine needs to be maintained for the common case — any byte
≤ 0x7F is forwarded immediately to USB CDC.

**Affects:** `03-uart-usb-hid-protocol.md`.

---

## D7 — CAN TX queue overflow: frame-type dependent

**Decision:** CAN TX overflow policy depends on frame type:

| Frame type | Policy |
|---|---|
| `CTRL_BCAST` DCS output broadcasts | Drop stale queued state and retain the newest frame. Coalesce by `controlId` where practical. |
| `EVT_n` input events | Bounded retry: keep the event for up to 3 send attempts, then drop it and increment the `DIAG_ERR` TX drop counter. Never build an unbounded backlog. |
| `HB_n` heartbeat | Drop stale heartbeat; the next heartbeat replaces it. |
| `READY_n`, `SYNC_REQ`, `TEST_SEQ`, `ECHO_n` | Bounded retry up to 3 attempts, then drop and increment the `DIAG_ERR` TX drop counter. |

**Rationale:** output broadcasts are state snapshots; the newest value is always more useful
than stale intermediate gauge/LED values. Input events are discrete user actions and should
not use stale-output drop-oldest semantics, but they also must not create an unbounded backlog
when the bus is unhealthy. Three attempts is enough to ride out transient mailbox contention;
if drops occur in normal traffic, the diagnostic counter exposes a bus/load problem.

**Affects:** `02-can-protocol.md`, `06-panelbridge-api.md`.

---

## D8 — ANALOG_NC = 0xFFFF

**Decision:** `AnalogMultiPos` uses `0xFFFF` as the sentinel for positions with no physical
detent.

**Rationale:** STM32 ADC tops at 65520 after ×16 scaling; ADS1115 tops at 65534 (its 0–3.3V
span is stretched onto the 16-bit range and clamped one under `0xFFFF` — #325). `0xFFFF` (65535)
is unreachable on both hardware paths. No separate
boolean is needed in the position array.

**Affects:** `05-panelgroup-api.md`.

---

## D9 — RotaryAcceleratedEncoder 4-value scheme (not delta + direction separately)

> **Superseded by #147.** The encoder rework moved variable-step knobs to REL — a signed `±step` on
> its own frame (`canIdEvtRel`) — and collapsed the input map to `controlId → name`, removing the
> `arg0`/`arg1`/`arg0fast`/`arg1fast` fields this scheme dispatched through. Acceleration is now a
> larger `±step` on the same REL frame, with no wire, bridge or map change; the class is a thin
> `RotaryEncoder` subclass under D16. Kept below for history.

**Decision (historical):** `RotaryAcceleratedEncoder` encodes both direction and speed into a single uint16
value: 0=slow CCW, 1=slow CW, 2=fast CCW, 3=fast CW. PanelBridge maps these to four
`DcsBiosInputEntry` arg fields.

**Rationale:** each `ControlPacket` carries only one value. Encoding direction+speed into
2 bits is compact and requires no additional struct fields in `ControlPacket`. The 4-value
scheme mirrors the DCS-BIOS Arduino library's accelerated encoder model exactly, avoiding any
mismatch between firmware and DCS-BIOS argument strings.

**Affects:** `05-panelgroup-api.md`, `04-dcs-bios-integration.md`.

---

## D10 — NODE_ID via PlatformIO build_flags

**Decision:** `NODE_ID` is declared as `build_flags = -DNODE_ID=3` in `platformio.ini`, not
as `#define NODE_ID 3` in `main.cpp`.

**Rationale:** a `#define` in `main.cpp` is visible only in that translation unit. The CAN
protocol library and other TUs need `NODE_ID` to compute frame IDs. `build_flags` injects it
as a compiler flag visible to all TUs in the project.

**Affects:** `02-can-protocol.md`, `05-panelgroup-api.md`.

---

## D11 — CAN batching via ControlPacketPair

**Decision:** `CTRL_BCAST` and `EVT_n` frames carry a `ControlPacketPair` so two
ControlPackets can share one 8-byte CAN frame. If only one packet is ready, slot B uses
`controlId = 0x0000` as the null sentinel. CANProtocol owns the batch builders and TX queue
state; PanelBridge and PanelGroup submit individual `ControlPacket`s. A half-full batch may
wait for slot B for at most two owning firmware `loop()` iterations after slot A is queued,
then it must be flushed with a null slot B. Here "cycle" means main firmware loop iteration,
not an MCU clock cycle.
Input snapshot bursts, such as boot and `SYNC_REQ` re-polls, flush any odd trailing slot-A
packet immediately at the end of the poll pass.

Batching is only required for input/output routing frames (`EVT_n` and `CTRL_BCAST`). Special
frames use their own explicitly defined DLC and payload. A future/special frame may carry a
single 4-byte `ControlPacket` without pairing, but that frame type must say so explicitly.

**Rationale:** batching uses the full classic CAN payload and cuts frame count for DCS output
bursts and input snapshot bursts without changing the simple `ControlPacket` routing model.
The null sentinel keeps single-packet sends trivial. The short batching deadline matters most
for `EVT_n` input traffic: user input should not sit in a half-full batch waiting for another
event that may not arrive.

**Affects:** `02-can-protocol.md`, `06-panelbridge-api.md`, `09-startup-resync-diagnostics.md`.

---

## D12 — HB_0 is reserved but not transmitted

**Decision:** `canIdHb(0)` (`0x100`) remains reserved by the CAN ID formula for PanelBridge,
but PanelBridge does not transmit a master heartbeat in normal firmware.

**Rationale:** PanelBridge is the CAN master and no production node consumes a master heartbeat.
Sending `HB_0` adds traffic and implementation surface without a receiver. PanelBridge health
is diagnosed through its own DiagSerial output and through the presence or absence of routed
CAN/DCS traffic.

**Affects:** `02-can-protocol.md`, `06-panelbridge-api.md`.

---

## D13 — Internal die-temp telemetry on a new HEALTH_n frame, uncalibrated, no default trip (#213)

**Decision:** every STM32 node reads its MCU internal temperature sensor (ADC ch16, using Vrefint
ch17 internally to reference the reading to Vdd) and reports `dieTempC` on a **new dedicated
`HEALTH_n` frame** (`0x140+n`, 1000 ms, default-on). It is **not** folded into `HB_n`. Vdd is
measured but **not transmitted** — per-node rail voltage is weak signal on a regulated bus and is
covered properly by the PDU's INA226 power telemetry (#202). The overheat flag / status-LED
WARNING is computed only when a build defines `NODE_OVERHEAT_C`; the default build ships pure
telemetry with no trip point. The frame is the shared node-health contract (#221): temperature
(#213) and degraded-state (#163) each own their own fields within the fixed 8 bytes.

**Rationale:**
- *New frame, not repack.* The 8-byte `HeartbeatPayload` is already full, and its consumers
  (PanelBridge tracking, the client's `_NODE_STATUS` parser) depend on its exact layout.
  A separate frame leaves that contract untouched and gives room for future health fields
  (3 reserved bytes). The `0x140–0x17F` range was free.
- *Free telemetry.* The sensor is on-die — no external parts, no schematic/BOM change — so the
  convention applies to every existing and future STM32 board unchanged.
- *No default trip.* The F103 sensor is uncalibrated (no factory trim) and reads die (not
  ambient) temperature with a self-heat offset, so a meaningful overheat threshold needs field
  data first. Shipping telemetry-only lets the fleet collect trend data before a trip point is
  chosen; enabling it is a one-line `-DNODE_OVERHEAT_C=N` opt-in.
- *STM32 only.* The RP2040 SimGateway is not on CAN and shares a PCB with PanelBridge, whose
  `HEALTH_0` already represents that board's thermal zone — a second sensor there is redundant.

**Affects:** `02-can-protocol.md`, `08-hardware-firmware-contracts.md`, `docs/_source/hardware-standards.md`,
`NodeStatus.h` (`_NODE_STATUS` proto v2 + `NodeFaultCode`), SkyHawkClient (host surfacing).

---

## D14 — Node status/fault: a neutral NodeStatus library + FaultSource registry (#163)

**Decision:** the cross-node **status** contract lives in a neutral `NodeStatus` library —
`NODE_STATUS_*` (the DCS-BIOS host-reporting contract), `NodeHealthFlag` (HEALTH_n flag bits),
`NodeFaultCode` (the wire faultId dictionary), and `FaultSource` (the interface a fault-producing
object implements). A fault-producing object (e.g. `DrumDisplay`, a future PDU rail monitor, a
PanelBridge host-link watchdog) **inherits `FaultSource`** and self-registers. A node-level
aggregator (`OpenSkyhawk::aggregateFaults()`, implemented in PR-3) walks `FaultSource::head()`,
picks the primary `NodeFaultCode` (first non-`NONE` in registry order) for `HEALTH_n.faultId`,
derives DEGRADED, and logs `faultDetail()` to **DiagSerial only** (edge-logged per node).
`NodeHealthPayload` (the CAN frame struct) stays in `CANProtocol.h`.

**Rationale:**
- *It's node **status**, not just health, and every node type has it* — PanelGroup, PanelBridge,
  and the PDU (#202) are all nodes. The vocabulary can't be shaped around one flavor (`PanelGroup`/
  `OutputBase`) or the HID namespace, and it's broader than "health" (it owns the `_NODE_STATUS`
  reporting layer). A neutral `NodeStatus` library every node depends on is the right home; the
  client syncs the whole contract from one place.
- *Fault sources feed a node aggregator; no producer "owns" node health.* `DrumDisplay` is **one**
  fault source ("I2C peripheral fault"), not special. A PDU reports over/under-voltage/short; a
  bridge reports host-link-lost. Modeling each as a `FaultSource` (self-registering, reporting
  cached `faultCode()` + local `faultDetail()`) keeps output/monitor classes decoupled and lets the
  fault vocabulary grow per node type. `OutputBase` gains **no** fault API.
- *Coarse, one-at-a-time faultId on the wire; device-detail strings stay local (DiagSerial), never
  over CAN and never in a shared/HID header.*

**Affects:** `NodeStatus.md` (new lib), `02-can-protocol.md`, `04-dcs-bios-integration.md`,
`05-panelgroup-api.md` (`OutputBase` has no fault API), `CANProtocol.h` (keeps `NodeHealthPayload`),
`DrumDisplay` (a `FaultSource`), SkyHawkClient#40 (fault-label table).

---

## D15 — ADC prescaler `/6` on spec grounds, not on a measured symptom (#263)

**Decision:** `STM32Board`'s strong `SystemClock_Config` sets `RCC_ADCPCLK2_DIV6` (APB2 72 MHz →
**ADCCLK 12 MHz**) on **both** of its exit paths. Previously nothing in the project wrote `ADCPRE`,
so it sat at its reset `/2` and the ADC ran at **36 MHz against the F103's 14 MHz maximum**. `/4` =
18 MHz is still out of spec, so `/6` is the fastest legal divider.

We are recording this as a decision **because the obvious justifications turned out to be false**,
and without this record the next person will re-derive and re-bench them.

**Rationale:**
- *Nobody owned the setting, and that is a structural fact, not an oversight to re-litigate.* On F1
  the STM32duino core deliberately delegates the ADC prescaler to `SystemClock_Config` (its
  `__HAL_RCC_ADC_CONFIG` is guarded `!defined(STM32F1xx)`), and `variant_generic.cpp` — the variant
  our #245 override displaces — never set it. `variant_PILL_F103Cx.cpp` *does*, via HAL, so this
  change is restoring a step the override dropped rather than inventing one. Use HAL
  (`HAL_RCCEx_PeriphCLKConfig`) to match both that variant and the rest of `STM32Board.cpp`.
- *Both exit paths, not one.* `SystemClock_Config` returns early on the verified 72 MHz path and
  falls through to an HSI-8 MHz fault path. A single write at the early `return` would leave
  `ADCPRE` at reset for every faulted board. Covered by `test_adc_clock` / `test_adc_clock_fallback`.

**Three predicted impacts were measured on the assembled PanelGroup Rev 1 and found ABSENT:**

| Predicted | Measured at 12 vs 36 MHz |
|---|---|
| Axis noise | 0 vs 1 emission per 100 s; smoothed p-p 24 vs 25 counts. Buffered hall outputs settle fine in the 375 ns that 13.5 cycles gives at 36 MHz. |
| PA2 under-settling | 4.3 % short of rail (177 LSB) at 36 MHz is real — but PA2 is a button, read digitally in production. |
| Die temperature | Predicted corrupt (sensor needs ≥17.1 µs; 239.5 cycles = 6.65 µs at 36 MHz). Read **34.0 °C at both clocks**; Vdd 3206 vs 3203 mV. |

An earlier "~3× noise improvement" figure came from a **breadboard**, whose contact resistance was
acting as a high source impedance. It does not transfer to a properly-wired board.

Rationale, continued:
- *So the honest justification is narrow:* the part was running 2.6× over its rated maximum, and
  high-impedance sources are susceptible in general — cockpit potentiometers sit at ~2.5 kΩ at
  mid-travel and should behave like PA2 by the same arithmetic. **That has never been measured on an
  actual pot.** No shipping analog input is known to be affected today. Do not let this change be
  described as fixing anything observable.
- *If someone wants to settle the pot question,* `Examples/E2E_DCS_Test/PanelGroupInputs` already
  wires ARC-51 VOL — a real pot — to PA2 as an `AnalogInput`; `Tests/PinRef/test_gpio_analog` on its
  10 kΩ + 10 kΩ divider is a second rig. Sample two channels, not one: a single channel leaves the
  sample-and-hold already at the right voltage, so settling is never stressed.
- *Cost accepted:* conversions take 3× longer (26 cycles: 0.72 µs → 2.17 µs; `analogRead()` ~56.5 µs
  → ~63 µs end-to-end, since its per-call calibration triples too). Irrelevant against
  `AnalogInput::POLL_MS` = 8 ms. `ADCPRE` feeds only the ADCs, so #245's CAN timing is untouched.

**Affects:** `08-hardware-firmware-contracts.md`, `STM32Board.md` (TechSpec — new *ADC clock
configuration* section, `begin()` diag-line format), `AnalogInput.md` (acquisition-time budget),
`STM32Board.cpp` (`_configAdcClock`), `Firmware/Tests/STM32Board` (two new envs).

---

## D16 — Control classes: two groups, class families, DCS-BIOS names (#286)

**Decision:** control classes sit in two groups — **Inputs** (`InputBase`) and **Outputs**
(`OutputBase`). Inside a group, related classes form a **family**: one base class holds the shared
behaviour, and thin subclasses change only the **source** (inputs) or the **sink** (outputs). The
precedent is `MultiPosInput` → `SwitchMultiPos` / `AnalogMultiPos`. Class names and behaviour follow
`dcs-bios-arduino-library` wherever an equivalent exists; where a class deliberately differs, its
TechSpec says why.

| Family base | Members | DCS-BIOS equivalent |
|---|---|---|
| `RotaryEncoder` | `RotaryAcceleratedEncoder` — momentum filter + `fastStep`; REL constructor (filter + speed) and DIR constructor (filter only) | `RotaryEncoder` / `RotaryAcceleratedEncoder` |
| `AnalogInput` | `AngleSensorInput` — angle meaning (degrees, 0°/360° wrap) on a `PinRef` source, through a protected virtual `readRaw()` | `Potentiometer` (no angle-sensor class) |
| `AnalogOutput` (abstract) | `Dimmer` (PWM duty), `IntegerOutput` (user callback); `ServoOutput` optional later | `Dimmer` / `IntegerBuffer` / `ServoOutput` |
| `Switch2Pos` | `SwitchWithCover2Pos` — one pin; sequences the cover before the switch | `SwitchWithCover2Pos` |

**Not ported: `DcsBios::RotarySwitch`.** It assumes position 0 at boot and sends absolute
`set_state` values, so the first click after a cold start can jump the sim away from a mission
preset. `RotaryEncoder` in DIR mode drives the same bounded selectors statelessly — DCS owns the
position and clamps at the ends — and DCS-BIOS's own M2000C radio examples use `RotaryEncoder`
INC/DEC for exactly those knobs.

**Rationale:**
- One decode / filter / emit path per family means one set of tests. A subclass is a constructor
  plus at most one override, so it adds nothing to the ISR or the loop hot path.
- Constructor length: `RotaryEncoder` already takes six positional arguments; putting the
  acceleration options on it would make eight, easy to pass in the wrong order. A subclass
  constructor makes the required arguments explicit (`fastStep` is required, `mode` is implied).
- DCS-BIOS parity lowers the barrier for builders who already know that library — the original
  plan was to "use dcs-bios-arduino-library as much as possible".

**Affects:** `05-panelgroup-api.md`, `10-implementation-plan.md`, TechSpec
(`RotaryAcceleratedEncoder`, `AngleSensor`, `AngleSensorInput`, `AnalogOutput`, `Dimmer`,
`IntegerOutput`, `SwitchWithCover2Pos`; `RotarySwitch` removed), `docs/firmware/control-types.md`.
