OpenSkyHawk/OpenSkyhawk/docs/assets/images/brand/project-3d-parts.png

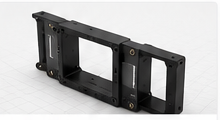
docs/assets/images/brand/project-3d-parts.png
