OpenSkyHawk/OpenSkyhawk/PCB/Right_Console/Right_Navigation/APN-153_Doppler/APN-153_Doppler.kicad_sch

## KiCad design PCB/Right_Console/Right_Navigation/APN-153_Doppler/APN-153_Doppler.kicad_sch (2026-07-10)

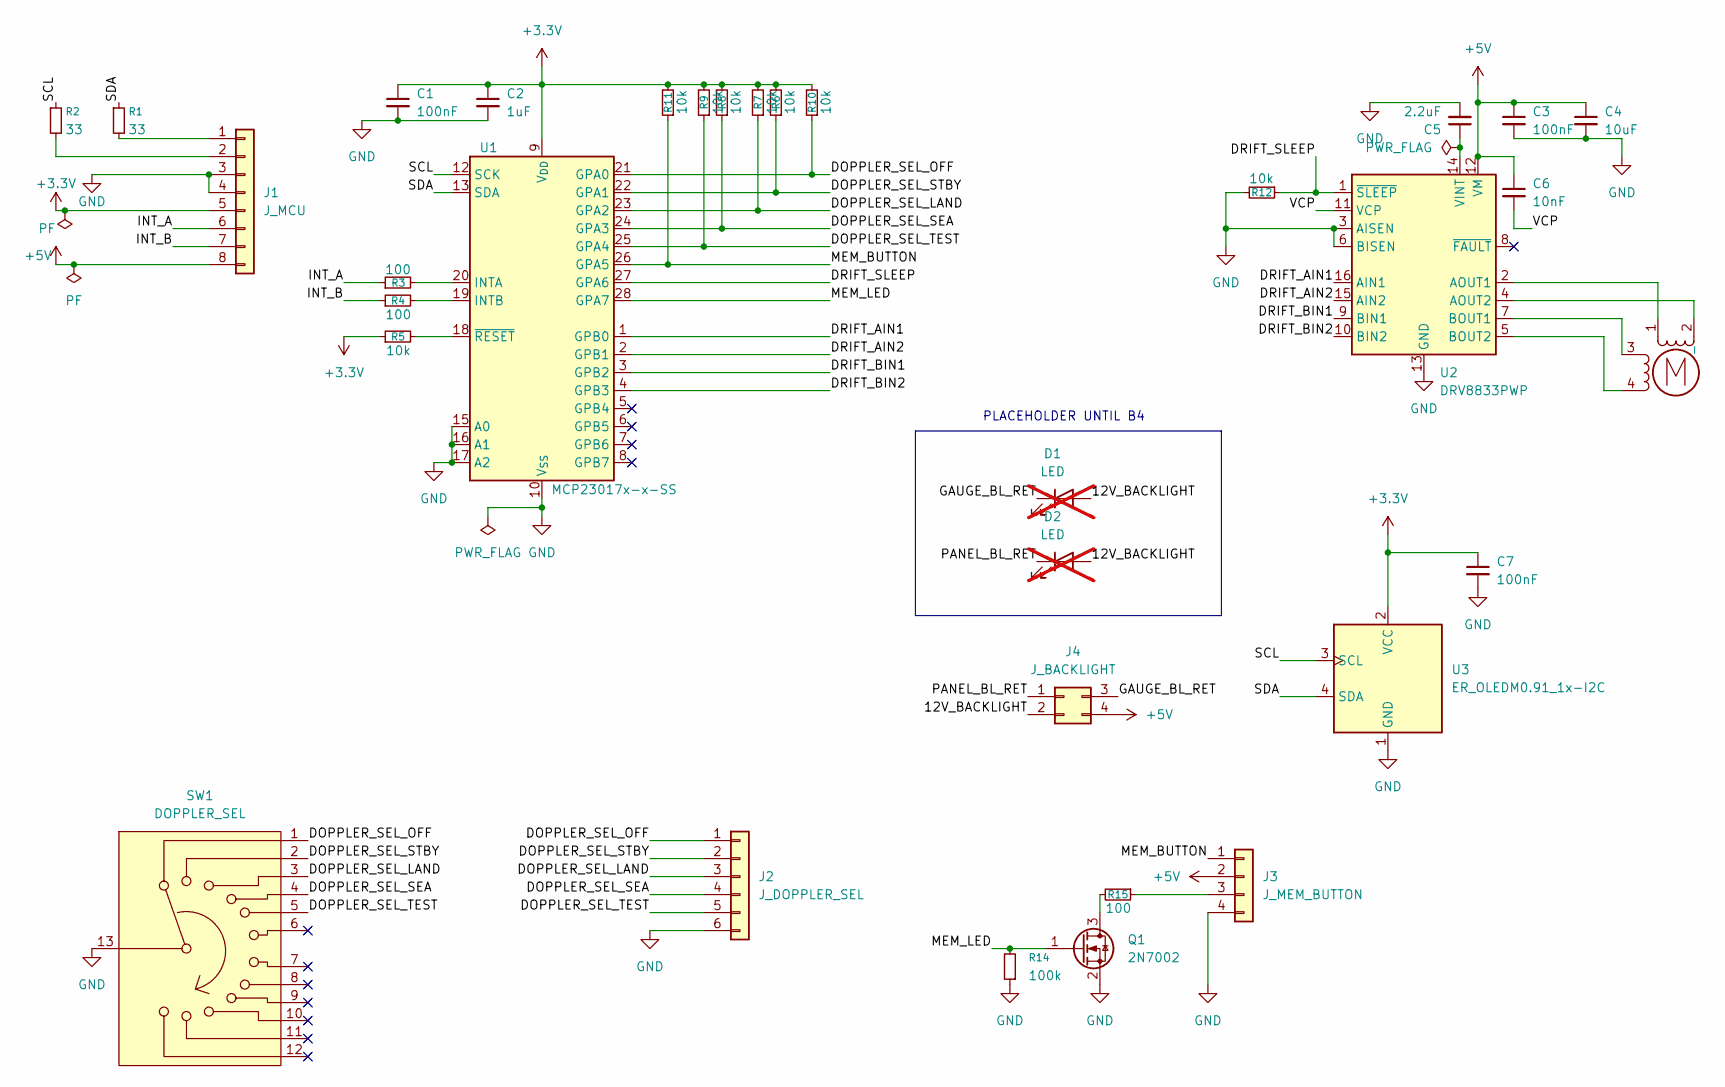
[picture p17: schematic APN-153_Doppler.kicad_sch]

Parts:
C1, C3, C7: 100nF; C_0805_2012Metric; Rating 50V; Tolerance 10%; LCSC C1711
C2: 1uF; C_0805_2012Metric; Rating 50V; Tolerance 10%; LCSC C28323
C4: 10uF; C_0805_2012Metric; Rating 35V; Tolerance 20%; LCSC C49010152
C5: 2.2uF; C_0805_2012Metric; Rating 25V; Tolerance 10%; LCSC C87994
C6: 10nF; C_0805_2012Metric; Rating 50V; Tolerance 10%; LCSC C1710
D1, D2: LED; LED_5050_Red; not fitted
J1: J_MCU; JST_XH_B8B-XH-A_1x08_P2.50mm_Vertical; LCSC C23067548
J2: J_DOPPLER_SEL; JST_XH_B6B-XH-A_1x06_P2.50mm_Vertical; LCSC C23067546
J3: J_MEM_BUTTON
J4: J_BACKLIGHT; Molex_Mini-Fit_Jr_5566-04A2_2x02_P4.20mm_Vertical; LCSC C20608114
MOT1: X27.589; X27.589_Stepper
Q1: 2N7002; SOT-23; Rating 60V; LCSC C8545
R1, R2: 33; R_0805_2012Metric; Rating 1/8W; Tolerance 1%; LCSC C2090807
R3, R4, R15: 100; R_0805_2012Metric; Rating 1/8W; Tolerance 1%; LCSC C844936
R5, R6, R7, R8, R9, R10, R11, R12: 10k; R_0805_2012Metric; Rating 1/8W; Tolerance 1%; LCSC C844937
R14: 100k; R_0805_2012Metric; Rating 1/8W; Tolerance 1%; LCSC C844935
SW1: DOPPLER_SEL
U1: MCP23017x-x-SS; SSOP-28_5.3x10.2mm_P0.65mm; LCSC C506653
U2: DRV8833PWP; HTSSOP-16-1EP_4.4x5mm_P0.65mm_EP3.4x5mm_Mask2.46x2.31mm_The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; LCSC C50506
U3: ER_OLEDM0.91_1x-I2C

Connections:
12V_BACKLIGHT: D1.2 (A), D2.2 (A), J4.2
+3.3V: C1.1, C2.1, C7.1, J1.5, R5.1, R6.2, R7.2, R8.2, R9.2, R10.2, R11.2, U1.9 (V_{DD}), U3.2 (VCC)
+5V: C3.1, C4.1, C6.1, J1.8, J3.2, J4.4, U2.12 (VM)
DOPPLER_SEL_LAND: J2.3, R7.1, SW1.3, U1.23 (GPA2)
DOPPLER_SEL_OFF: J2.1, R10.1, SW1.1, U1.21 (GPA0)
DOPPLER_SEL_SEA: J2.4, R8.1, SW1.4, U1.24 (GPA3)
DOPPLER_SEL_STBY: J2.2, R6.1, SW1.2, U1.22 (GPA1)
DOPPLER_SEL_TEST: J2.5, R9.1, SW1.5, U1.25 (GPA4)
DRIFT_AIN1: U1.1 (GPB0), U2.16 (AIN1)
DRIFT_AIN2: U1.2 (GPB1), U2.15 (AIN2)
DRIFT_BIN1: U1.3 (GPB2), U2.9 (BIN1)
DRIFT_BIN2: U1.4 (GPB3), U2.10 (BIN2)
DRIFT_SLEEP: R12.1, U1.27 (GPA6), U2.1 (~SLEEP)
GAUGE_BL_RET: D1.1 (K), J4.3
GND: C1.2, C2.2, C3.2, C4.2, C5.2, C7.2, J1.3, J1.4, J2.6, J3.4, Q1.2 (S), R12.2, R14.1, SW1.13, U1.10 (V_{SS}), U1.15 (A0), U1.16 (A1), U1.17 (A2), U2.3 (AISEN), U2.6 (BISEN), U2.13 (GND), U2.17 (GND), U3.1 (GND)
INT_A: J1.6, R3.1
INT_B: J1.7, R4.1
MEM_BUTTON: J3.1, R11.1, U1.26 (GPA5)
MEM_LED: Q1.1 (G), R14.2, U1.28 (GPA7)
unnamed: C5.1, U2.14 (VINT)
unnamed: J1.1, R1.2
unnamed: J1.2, R2.2
unnamed: J3.3, R15.1
unnamed: MOT1.1, U2.2 (AOUT1)
unnamed: MOT1.2 (-), U2.4 (AOUT2)
unnamed: MOT1.3, U2.7 (BOUT1)
unnamed: MOT1.4, U2.5 (BOUT2)
unnamed: Q1.3 (D), R15.2
unnamed: R3.2, U1.20 (INTA)
unnamed: R4.2, U1.19 (INTB)
unnamed: R5.2, U1.18 (~RESET)
PANEL_BL_RET: D2.1 (K), J4.1
SCL: R2.1, U1.12 (SCK), U3.3 (SCL)
SDA: R1.1, U1.13 (SDA), U3.4 (SDA)
VCP: C6.2, U2.11 (VCP)

Notes on the sheet:
PLACEHOLDER UNTIL B4
