OpenSkyHawk/OpenSkyhawk/PCB/Right_Console/Right_Navigation/ARC-51A_UHF/ARC-51A_UHF.kicad_sch

## KiCad design PCB/Right_Console/Right_Navigation/ARC-51A_UHF/ARC-51A_UHF.kicad_sch (2026-07-10)

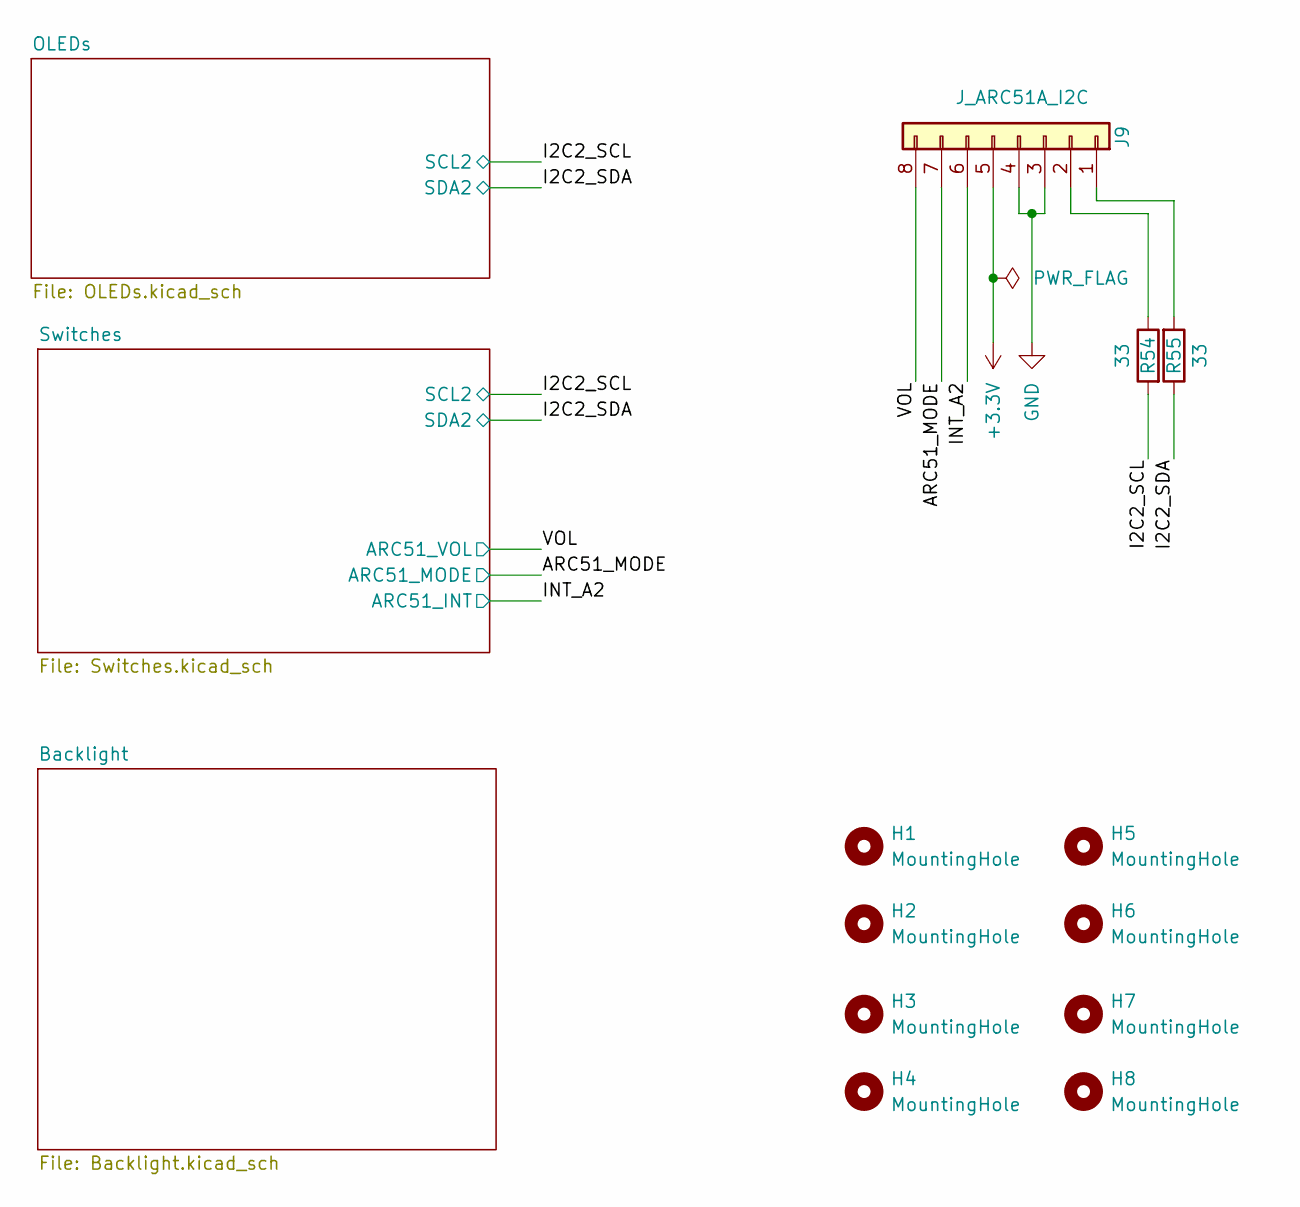
[picture p18: schematic ARC-51A_UHF.kicad_sch]

Parts:
H1, H2, H3, H4, H5, H6, H7, H8: MountingHole; MountingHole_2.7mm_M2.5
J9: J_ARC51A_I2C; JST_XH_B8B-XH-A_1x08_P2.50mm_Vertical; LCSC C23067548
R54, R55: 33; R_0805_2012Metric; Tolerance 1%; Rating 1/8W; LCSC C2090807

Connections:
+3.3V: J9.5
ARC51_MODE: J9.7
GND: J9.3, J9.4
I2C2_SCL: R54.2
I2C2_SDA: R55.1
INT_A2: J9.6
unnamed: J9.1, R55.2
unnamed: J9.2, R54.1
VOL: J9.8
