OpenSkyHawk/OpenSkyhawk/PCB/Right_Console/Right_Navigation/ARC-51A_UHF/Backlight.kicad_sch

## KiCad design PCB/Right_Console/Right_Navigation/ARC-51A_UHF/Backlight.kicad_sch (2026-07-10)

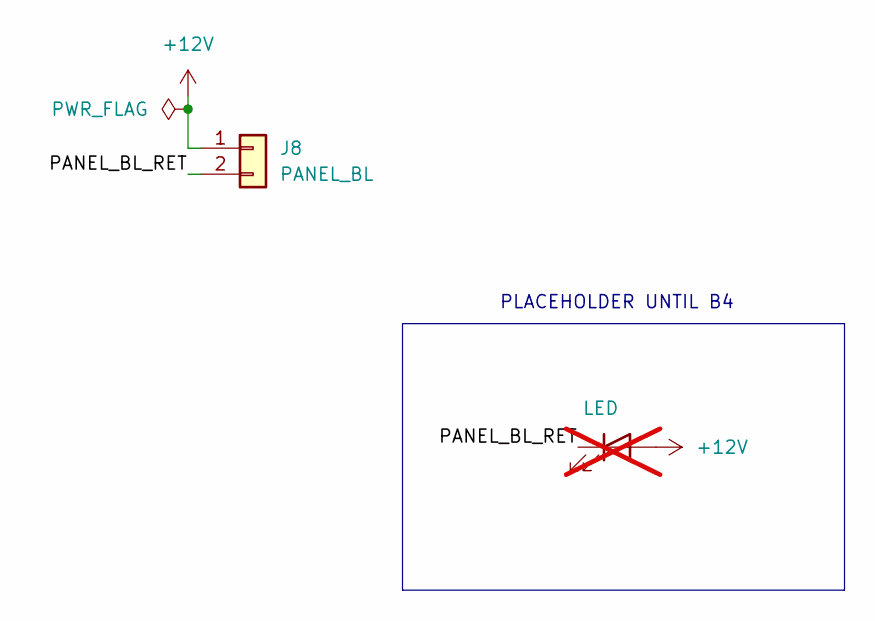
[picture p19: schematic Backlight.kicad_sch]

Parts:
D2: LED; LED_5050_Red; not fitted
J8: PANEL_BL; Molex_Mini-Fit_Jr_5566-02A_2x01_P4.20mm_Vertical; LCSC C20608113

Connections:
+12V: D2.2 (A), J8.1
PANEL_BL_RET: D2.1 (K), J8.2

Notes on the sheet:
PLACEHOLDER UNTIL B4
