OpenSkyHawk/OpenSkyhawk/PCB/Right_Console/Right_Navigation/ARC-51A_UHF/OLEDs.kicad_sch

## KiCad design PCB/Right_Console/Right_Navigation/ARC-51A_UHF/OLEDs.kicad_sch (2026-07-10)

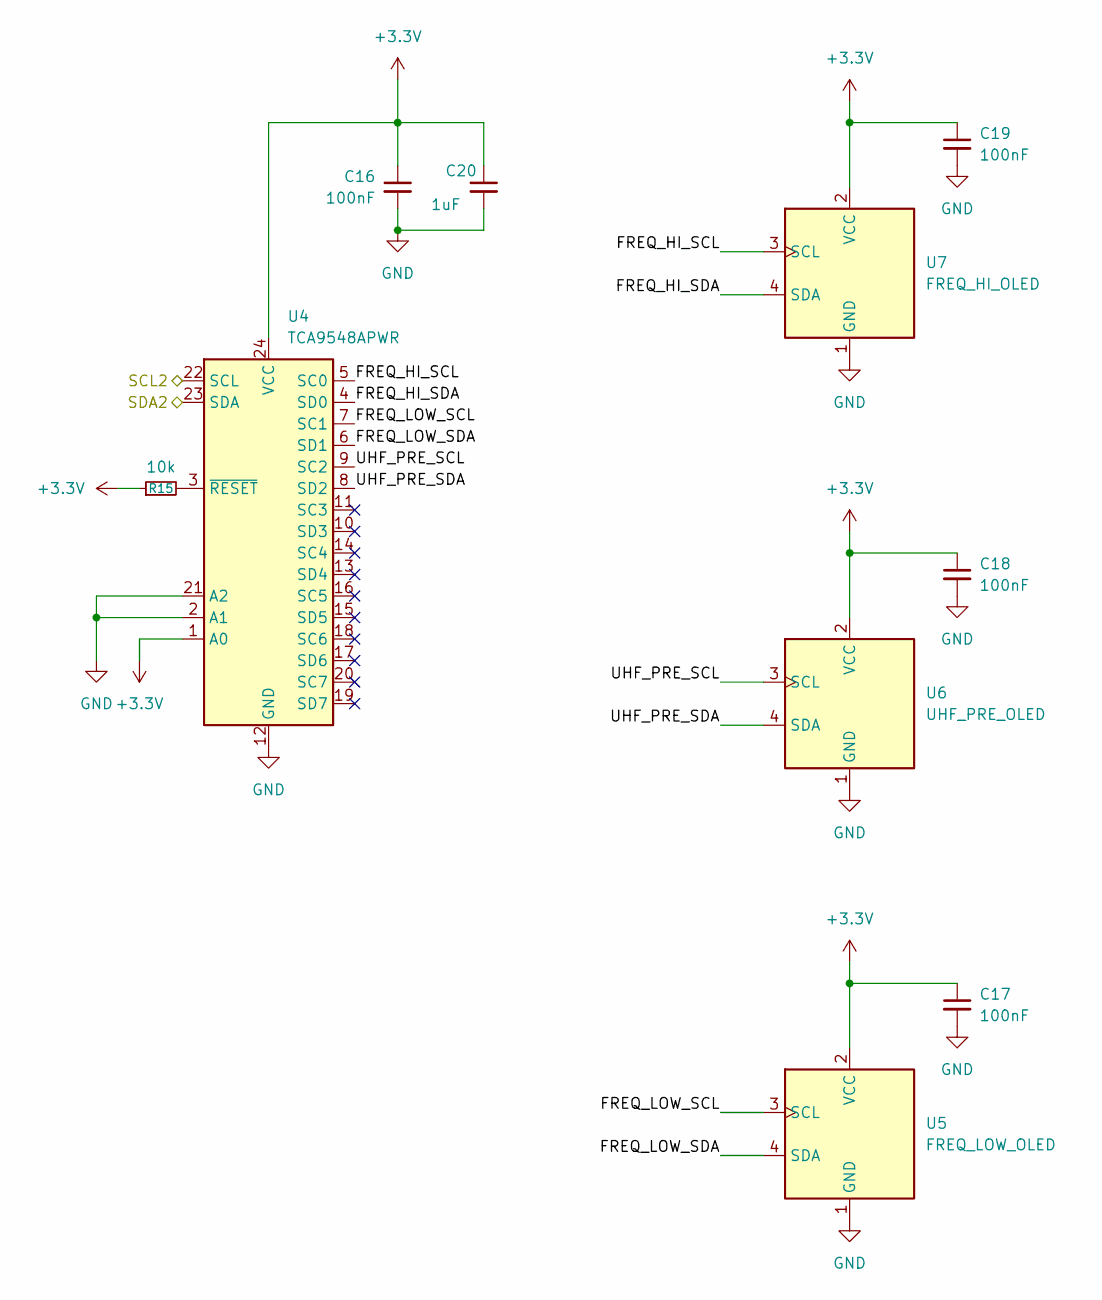
[picture p20: schematic OLEDs.kicad_sch]

Parts:
C16, C17, C18, C19: 100nF; C_0805_2012Metric; Tolerance 10%; Rating 50V; LCSC C1711
C20: 1uF; C_0805_2012Metric; Tolerance 10%; Rating 50V; LCSC C28323
R15: 10k; R_0805_2012Metric; Tolerance 1%; Rating 1/8W; LCSC C844937
U4: TCA9548APWR; TSSOP-24_4.4x7.8mm_P0.65mm; LCSC C130026
U5: FREQ_LOW_OLED; ER_OLEDM0.91_1x-I2C
U6: UHF_PRE_OLED; ER_OLEDM0.91_1x-I2C
U7: FREQ_HI_OLED; ER_OLEDM0.91_1x-I2C

Connections:
+3.3V: C16.1, C17.1, C18.1, C19.1, C20.1, R15.1, U4.1 (A0), U4.24 (VCC), U5.2 (VCC), U6.2 (VCC), U7.2 (VCC)
FREQ_HI_SCL: U4.5 (SC0), U7.3 (SCL)
FREQ_HI_SDA: U4.4 (SD0), U7.4 (SDA)
FREQ_LOW_SCL: U4.7 (SC1), U5.3 (SCL)
FREQ_LOW_SDA: U4.6 (SD1), U5.4 (SDA)
GND: C16.2, C17.2, C18.2, C19.2, C20.2, U4.2 (A1), U4.12 (GND), U4.21 (A2), U5.1 (GND), U6.1 (GND), U7.1 (GND)
unnamed: R15.2, U4.3 (~RESET)
SCL2: U4.22 (SCL)
SDA2: U4.23 (SDA)
UHF_PRE_SCL: U4.9 (SC2), U6.3 (SCL)
UHF_PRE_SDA: U4.8 (SD2), U6.4 (SDA)
