OpenSkyHawk/OpenSkyhawk/PCB/Right_Console/Right_Navigation/ARC-51A_UHF/Switches.kicad_sch

## KiCad design PCB/Right_Console/Right_Navigation/ARC-51A_UHF/Switches.kicad_sch (2026-07-10)

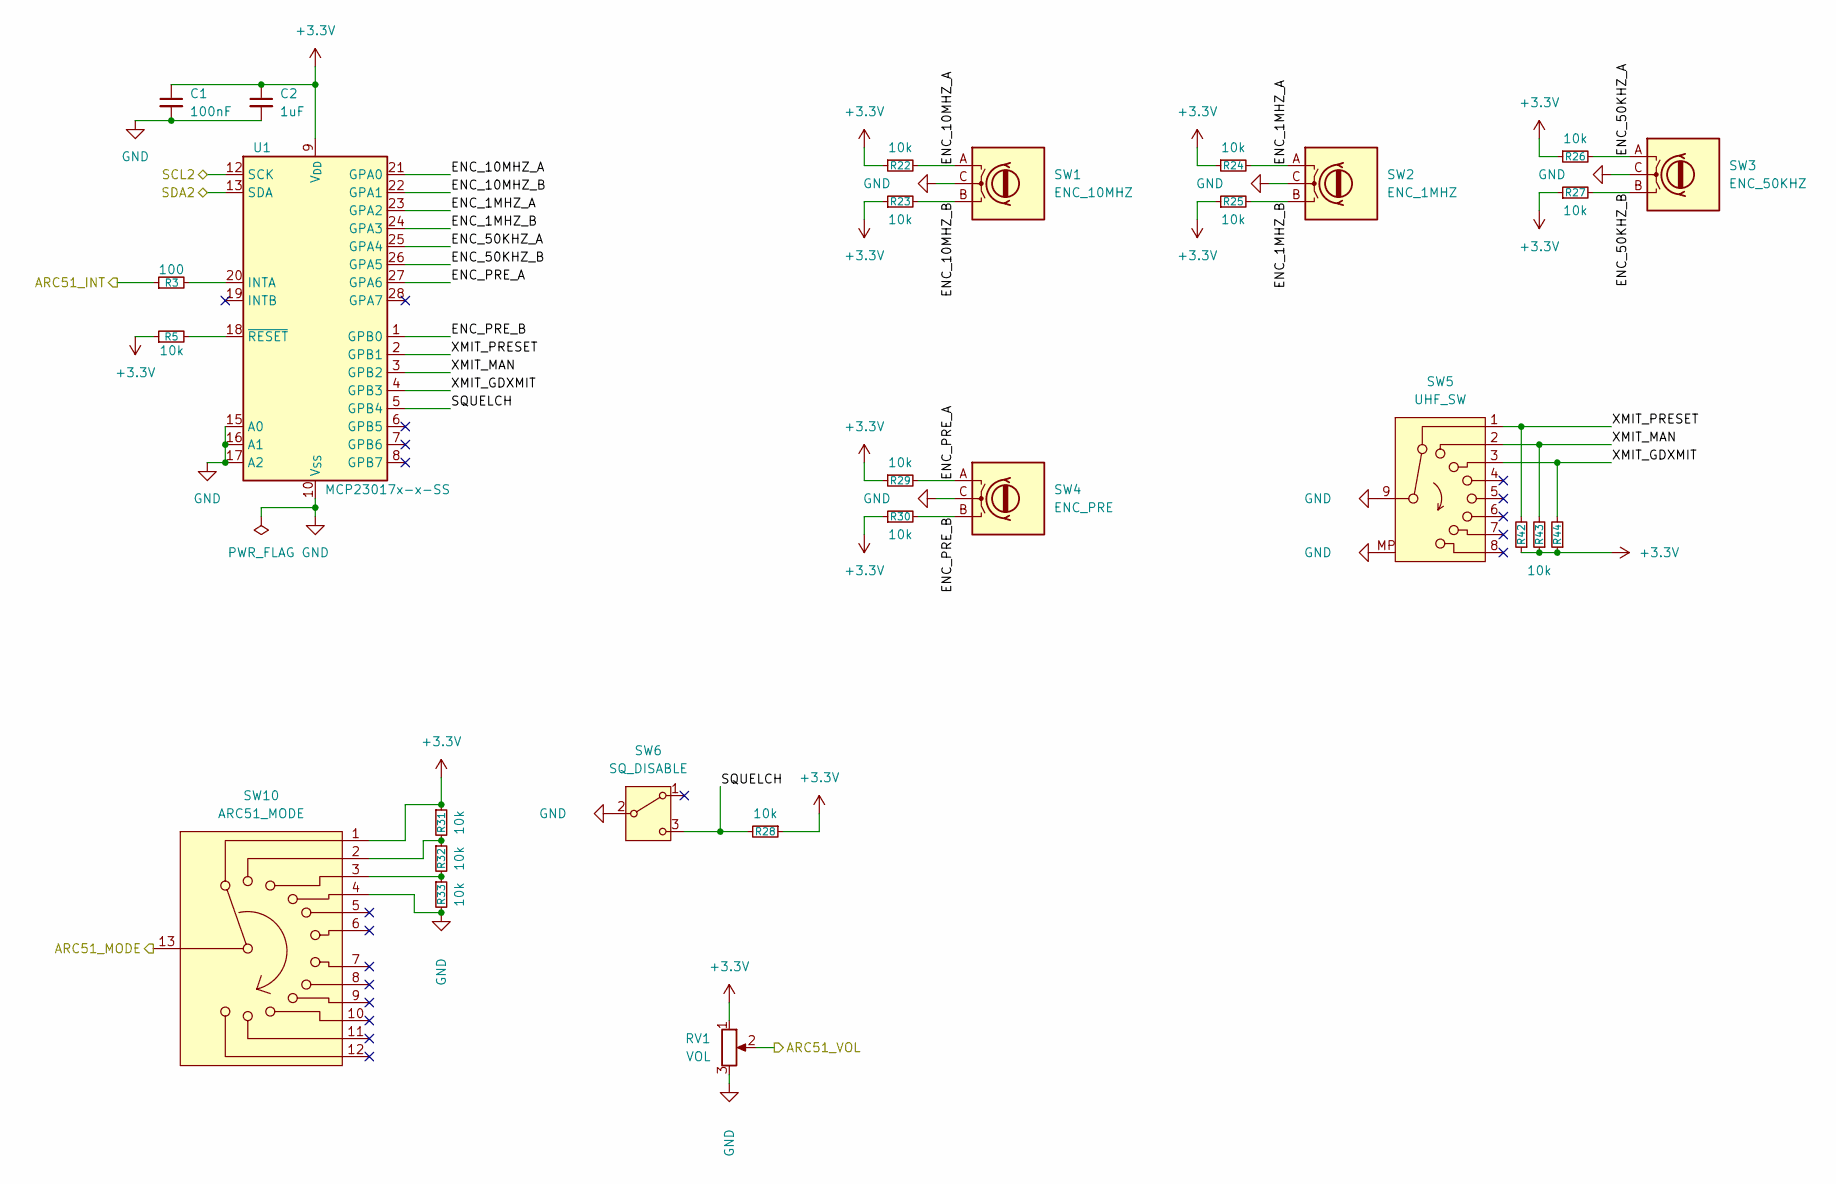
[picture p21: schematic Switches.kicad_sch]

Parts:
C1: 100nF; C_0805_2012Metric; Tolerance 10%; Rating 50V; LCSC C1711
C2: 1uF; C_0805_2012Metric; Tolerance 10%; Rating 50V; LCSC C28323
R3: 100; R_0805_2012Metric; Tolerance 1%; Rating 1/8W; LCSC C844936
R5, R22, R23, R24, R25, R26, R27, R28, R29, R30, R31, R32, R33, R42, R43, R44: 10k; R_0805_2012Metric; Tolerance 1%; Rating 1/8W; LCSC C844937
RV1: VOL
SW1: ENC_10MHZ
SW2: ENC_1MHZ
SW3: ENC_50KHZ
SW4: ENC_PRE
SW5: UHF_SW
SW6: SQ_DISABLE
SW10: ARC51_MODE
U1: MCP23017x-x-SS; SSOP-28_5.3x10.2mm_P0.65mm; LCSC C506653

Connections:
+3.3V: C1.1, C2.1, R5.1, R22.1, R23.1, R24.1, R25.1, R26.1, R27.1, R28.1, R29.1, R30.1, R31.1, R42.1, R43.1, R44.1, RV1.1, SW10.1, U1.9 (V_{DD})
ARC51_INT: R3.1
ARC51_MODE: SW10.13
ARC51_VOL: RV1.2
ENC_1MHZ_A: R24.2, SW2.A, U1.23 (GPA2)
ENC_1MHZ_B: R25.2, SW2.B, U1.24 (GPA3)
ENC_10MHZ_A: R22.2, SW1.A, U1.21 (GPA0)
ENC_10MHZ_B: R23.2, SW1.B, U1.22 (GPA1)
ENC_50KHZ_A: R26.2, SW3.A, U1.25 (GPA4)
ENC_50KHZ_B: R27.2, SW3.B, U1.26 (GPA5)
ENC_PRE_A: R29.2, SW4.A, U1.27 (GPA6)
ENC_PRE_B: R30.2, SW4.B, U1.1 (GPB0)
GND: C1.2, C2.2, R33.2, RV1.3, SW1.C, SW2.C, SW3.C, SW4.C, SW5.9, SW5.MP, SW6.2 (B), SW10.4, U1.10 (V_{SS}), U1.15 (A0), U1.16 (A1), U1.17 (A2)
unnamed: R3.2, U1.20 (INTA)
unnamed: R5.2, U1.18 (~RESET)
unnamed: R31.2, R32.1, SW10.2
unnamed: R32.2, R33.1, SW10.3
SCL2: U1.12 (SCK)
SDA2: U1.13 (SDA)
SQUELCH: R28.2, SW6.3 (C), U1.5 (GPB4)
XMIT_GDXMIT: R44.2, SW5.3, U1.4 (GPB3)
XMIT_MAN: R43.2, SW5.2, U1.3 (GPB2)
XMIT_PRESET: R42.2, SW5.1, U1.2 (GPB1)
