OpenSkyHawk/OpenSkyhawk/PCB/Right_Console/Right_Navigation/ASN-41_NavComputer/Backlight.kicad_sch

## KiCad design PCB/Right_Console/Right_Navigation/ASN-41_NavComputer/Backlight.kicad_sch (2026-07-10)

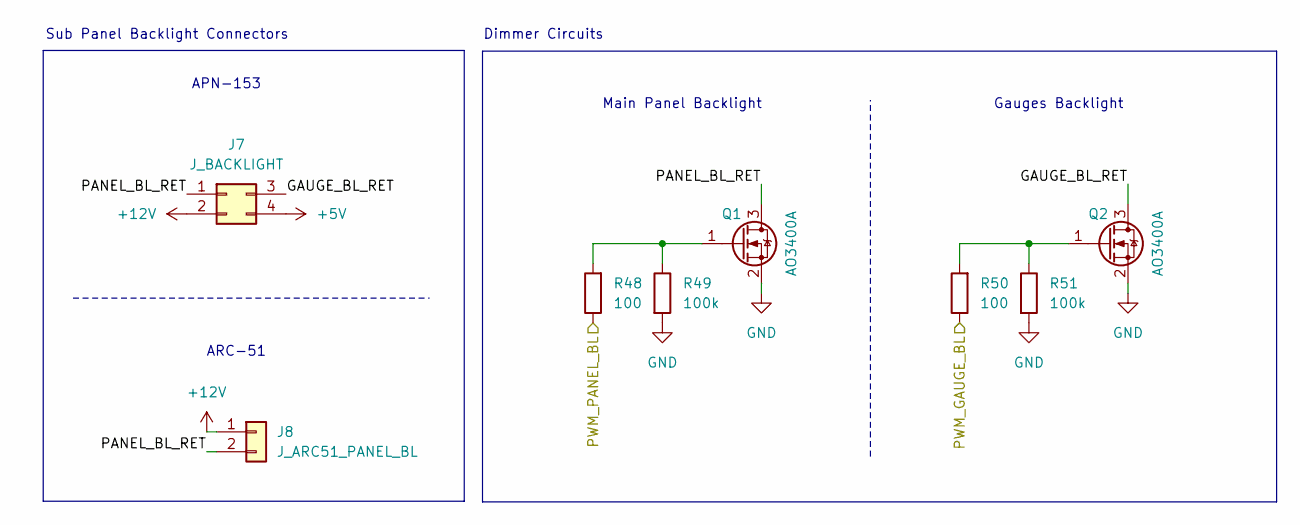
[picture p22: schematic Backlight.kicad_sch]

Parts:
J7: J_BACKLIGHT; Molex_Mini-Fit_Jr_5566-04A2_2x02_P4.20mm_Vertical; LCSC C20608114
J8: J_ARC51_PANEL_BL; Molex_Mini-Fit_Jr_5566-02A_2x01_P4.20mm_Vertical; LCSC C20608113
Q1, Q2: AO3400A; SOT-23; Rating 30V; LCSC C49195711
R48, R50: 100; R_0805_2012Metric; Tolerance 1%; Rating 1/8W; LCSC C844936
R49, R51: 100k; R_0805_2012Metric; Tolerance 1%; Rating 1/8W; LCSC C844935

Connections:
+5V: J7.4
+12V: J7.2, J8.1
GAUGE_BL_RET: J7.3, Q2.3
GND: Q1.2, Q2.2, R49.2, R51.2
unnamed: Q1.1, R48.2, R49.1
unnamed: Q2.1, R50.2, R51.1
PANEL_BL_RET: J7.1, J8.2, Q1.3
PWM_GAUGE_BL: R50.1
PWM_PANEL_BL: R48.1

Notes on the sheet:
Sub Panel Backlight Connectors
Gauges Backlight
Dimmer Circuits
APN-153
ARC-51
Main Panel Backlight
