OpenSkyHawk/OpenSkyhawk/PCB/Right_Console/Right_Navigation/ASN-41_NavComputer/MCU.kicad_sch

## KiCad design PCB/Right_Console/Right_Navigation/ASN-41_NavComputer/MCU.kicad_sch (2026-07-11)

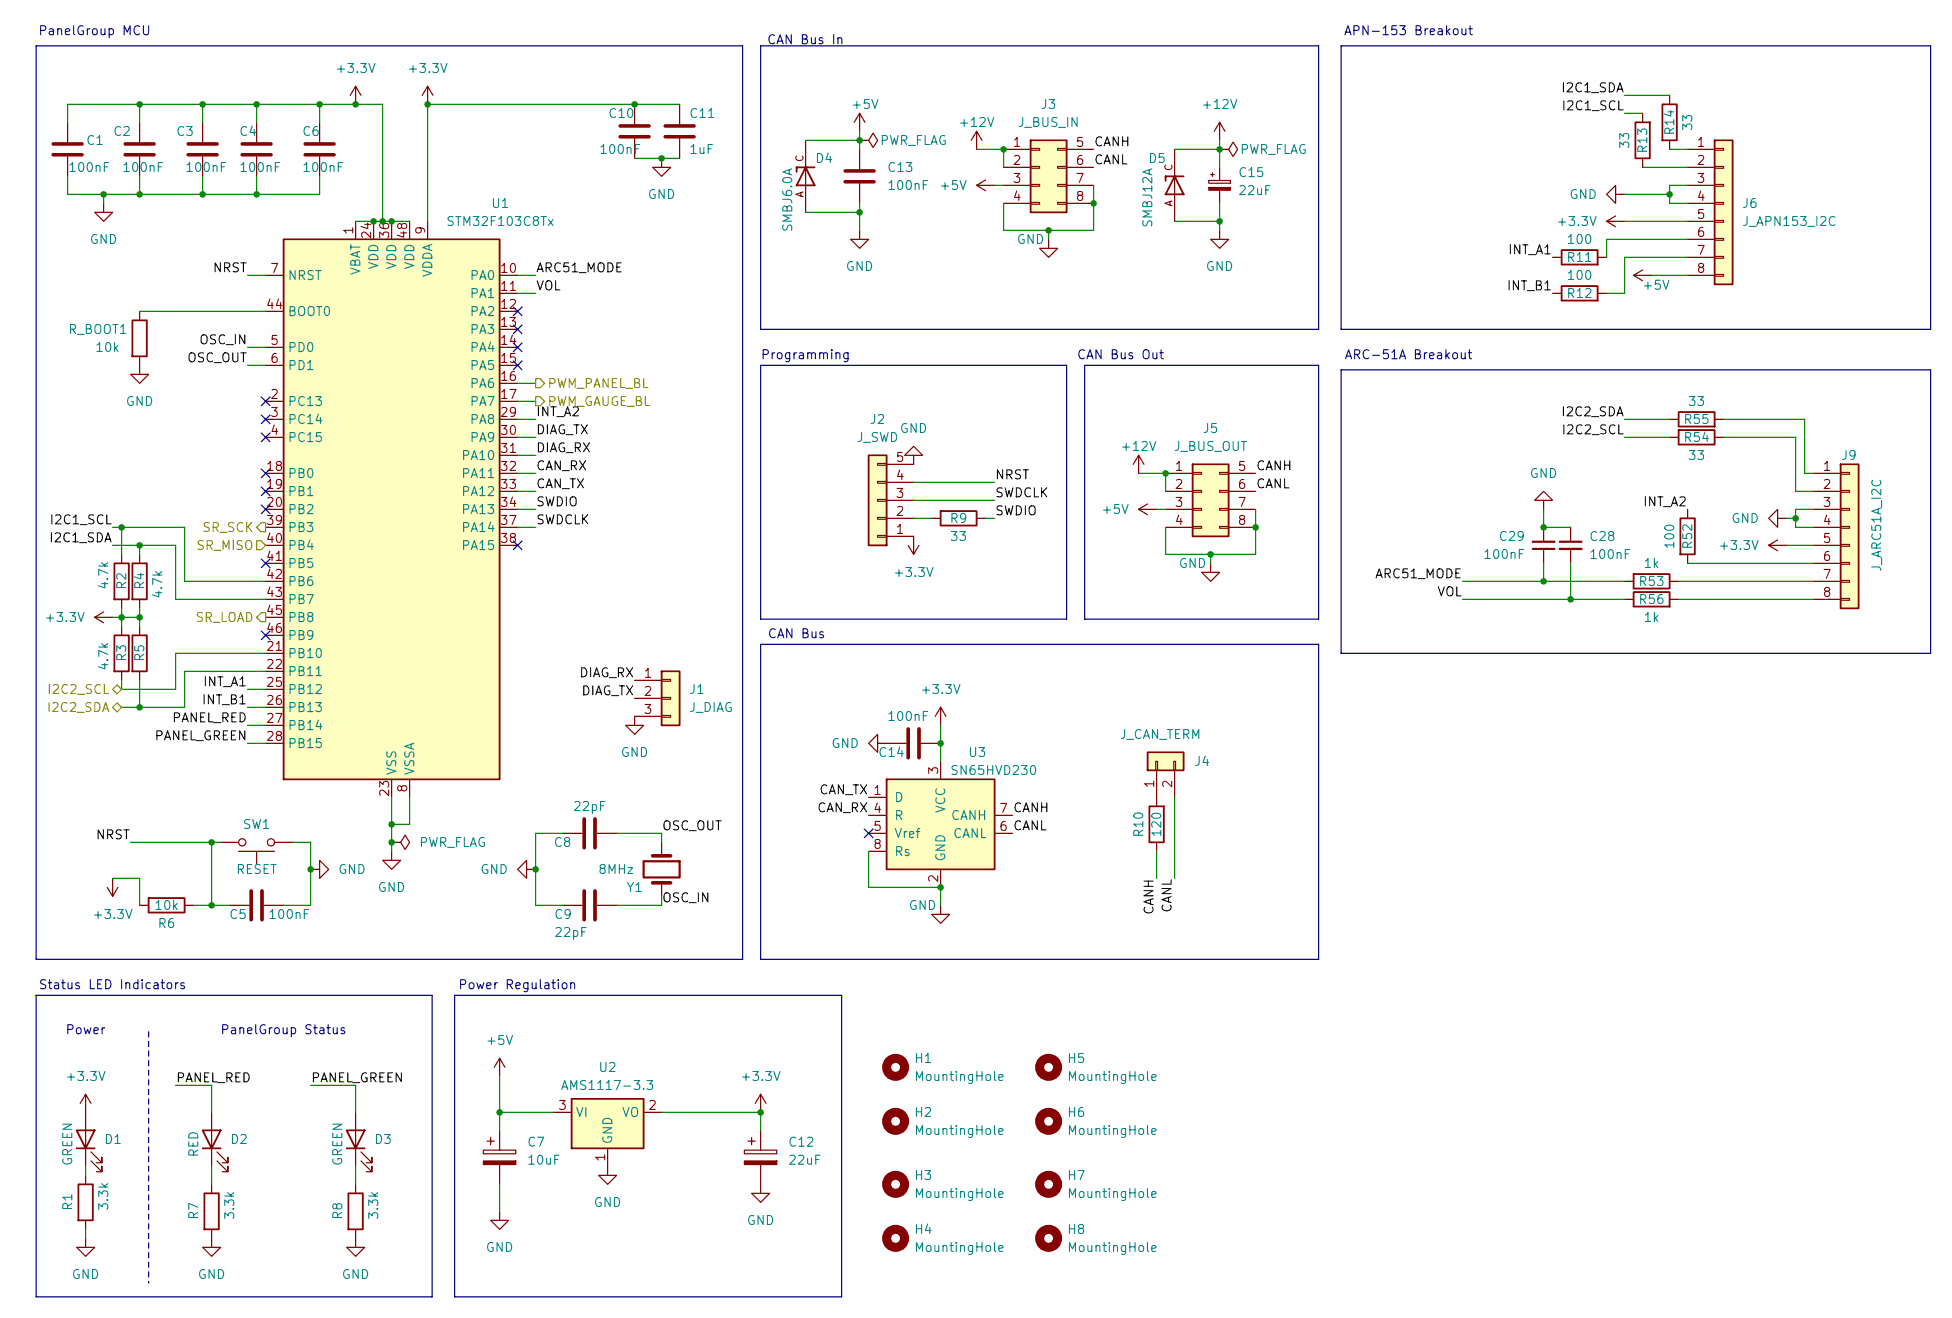
[picture p23: schematic MCU.kicad_sch]

Parts:
C1, C2, C3, C4, C5, C6, C10, C13, C14, C28, C29: 100nF; C_0805_2012Metric; Tolerance 10%; Rating 50V; LCSC C1711
C7: 10uF; CP_Elec_4x5.4; Tolerance 20%; Rating 25V; LCSC C3343
C8, C9: 22pF; C_0805_2012Metric; Tolerance 5%; Rating 50V; LCSC C1804
C11: 1uF; C_0805_2012Metric; Tolerance 10%; Rating 50V; LCSC C28323
C12: 22uF; CP_Elec_4x5.4; Tolerance 20%; Rating 16V; LCSC C72502
C15: 22uF; CP_Elec_5x5.4; Rating 35V; Tolerance 20%; LCSC C48971029
D1, D3: GREEN; LED_0805_2012Metric; LCSC C19171393
D2: RED; LED_0805_2012Metric; LCSC C19171391
D4: SMBJ6.0A; DIOM4336X265N; PARTREV F2102; LCSC C5331096
D5: SMBJ12A; DIOM4336X265N; PARTREV F2102; LCSC C42368008
H1, H2, H3, H4, H5, H6, H7, H8: MountingHole; MountingHole_2.7mm_M2.5
J1: J_DIAG; JST_XH_B3B-XH-A_1x03_P2.50mm_Vertical; LCSC C51940188
J2: J_SWD; PinHeader_1x05_P2.54mm_Vertical
J3: J_BUS_IN; Molex_Mini-Fit_Jr_5566-08A_2x04_P4.20mm_Vertical; LCSC C20608116
J4: J_CAN_TERM; PinHeader_1x02_P2.54mm_Vertical
J5: J_BUS_OUT; Molex_Mini-Fit_Jr_5566-08A_2x04_P4.20mm_Vertical; LCSC C20608116
J6: J_APN153_I2C; JST_XH_B8B-XH-A_1x08_P2.50mm_Vertical; LCSC C23067548
J9: J_ARC51A_I2C; JST_XH_B8B-XH-A_1x08_P2.50mm_Vertical; LCSC C23067548
R1, R7, R8: 3.3k; R_0805_2012Metric; Tolerance 1%; Rating 1/8W; LCSC C844412
R2, R3, R4, R5: 4.7k; R_0805_2012Metric; Tolerance 1%; Rating 1/8W; LCSC C844941
R6: 10k; R_0805_2012Metric; Tolerance 1%; Rating 1/8W; LCSC C844937
R9, R13, R14, R54, R55: 33; R_0805_2012Metric; Tolerance 1%; Rating 1/8W; LCSC C2090807
R10: 120; R_0805_2012Metric; Tolerance 1%; Rating 1/8W; LCSC C844816
R11, R12, R52: 100; R_0805_2012Metric; Tolerance 1%; Rating 1/8W; LCSC C844936
R53, R56: 1k; R_0805_2012Metric; Tolerance 1%; Rating 1/8W; LCSC C844939
R_BOOT1: 10k; R_0805_2012Metric; Tolerance 1%; Rating 1/8W; LCSC C844937
SW1: RESET; SW_PUSH_6mm; LCSC C2939600
U1: STM32F103C8Tx; LQFP-48_7x7mm_P0.5mm; LCSC C8734
U2: AMS1117-3.3; SOT-223-3_TabPin2; LCSC C347222
U3: SN65HVD230; SOIC-8_3.9x4.9mm_P1.27mm; LCSC C12084
Y1: 8MHz; Crystal_SMD_5032-2Pin_5.0x3.2mm; LCSC C20617997

Connections:
+3.3V: C1.1, C2.1, C3.1, C4.1, C6.1, C10.1, C11.1, C12.1, C14.1, D1.2 (A), J2.1, J6.5, J9.5, R2.2, R3.1, R4.2, R5.1, R6.2, U1.1 (VBAT), U1.9 (VDDA), U1.24 (VDD), U1.36 (VDD), U1.48 (VDD), U2.2 (VO), U3.3 (VCC)
+5V: C7.1, C13.1, D4.C, J3.3, J5.3, J6.8, U2.3 (VI)
+12V: C15.1, D5.C, J3.1, J3.2, J5.1, J5.2
ARC51_MODE: C29.1, R53.2, U1.10 (PA0)
CANH: J3.5, J5.5, R10.1, U3.7 (CANH)
CANL: J3.6, J4.2, J5.6, U3.6 (CANL)
CAN_RX: U1.32 (PA11), U3.4 (R)
CAN_TX: U1.33 (PA12), U3.1 (D)
DIAG_RX: J1.1, U1.31 (PA10)
DIAG_TX: J1.2, U1.30 (PA9)
GND: C1.2, C2.2, C3.2, C4.2, C5.2, C6.2, C7.2, C8.1, C9.2, C10.2, C11.2, C12.2, C13.2, C14.2, C15.2, C28.1, C29.2, D4.A, D5.A, J1.3, J2.5, J3.4, J3.7, J3.8, J5.4, J5.7, J5.8, J6.3, J6.4, J9.3, J9.4, R1.2, R7.2, R8.2, R_BOOT1.2, SW1.1, U1.8 (VSSA), U1.23 (VSS), U1.35 (VSS), U1.47 (VSS), U2.1 (GND), U3.2 (GND), U3.8 (Rs)
I2C1_SCL: R2.1, R13.2, U1.42 (PB6)
I2C1_SDA: R4.1, R14.1, U1.43 (PB7)
I2C2_SCL: R3.2, R54.2, U1.21 (PB10)
I2C2_SDA: R5.2, R55.1, U1.22 (PB11)
INT_A1: R11.1, U1.25 (PB12)
INT_A2: R52.1, U1.29 (PA8)
INT_B1: R12.1, U1.26 (PB13)
NRST: C5.1, J2.4, R6.1, SW1.2, U1.7 (NRST)
unnamed: D1.1 (K), R1.1
unnamed: D2.1 (K), R7.1
unnamed: D3.1 (K), R8.1
unnamed: J2.2, R9.2
unnamed: J4.1, R10.2
unnamed: J6.1, R14.2
unnamed: J6.2, R13.1
unnamed: J6.6, R11.2
unnamed: J6.7, R12.2
unnamed: J9.1, R55.2
unnamed: J9.2, R54.1
unnamed: J9.6, R52.2
unnamed: J9.7, R53.1
unnamed: J9.8, R56.2
unnamed: R_BOOT1.1, U1.44 (BOOT0)
OSC_IN: C9.1, U1.5 (PD0), Y1.2
OSC_OUT: C8.2, U1.6 (PD1), Y1.1
PANEL_GREEN: D3.2 (A), U1.28 (PB15)
PANEL_RED: D2.2 (A), U1.27 (PB14)
PWM_GAUGE_BL: U1.17 (PA7)
PWM_PANEL_BL: U1.16 (PA6)
SR_LOAD: U1.45 (PB8)
SR_MISO: U1.40 (PB4)
SR_SCK: U1.39 (PB3)
SWDCLK: J2.3, U1.37 (PA14)
SWDIO: R9.1, U1.34 (PA13)
VOL: C28.2, R56.1, U1.11 (PA1)

Notes on the sheet:
CAN Bus
CAN Bus In
Status LED Indicators
Power
Power Regulation
Programming
PanelGroup MCU
PanelGroup Status
ARC-51A Breakout
APN-153 Breakout
CAN Bus Out
