OpenSkyHawk/OpenSkyhawk/PCB/Right_Console/Right_Navigation/ASN-41_NavComputer/Oled_Displays.kicad_sch

## KiCad design PCB/Right_Console/Right_Navigation/ASN-41_NavComputer/Oled_Displays.kicad_sch (2026-07-10)

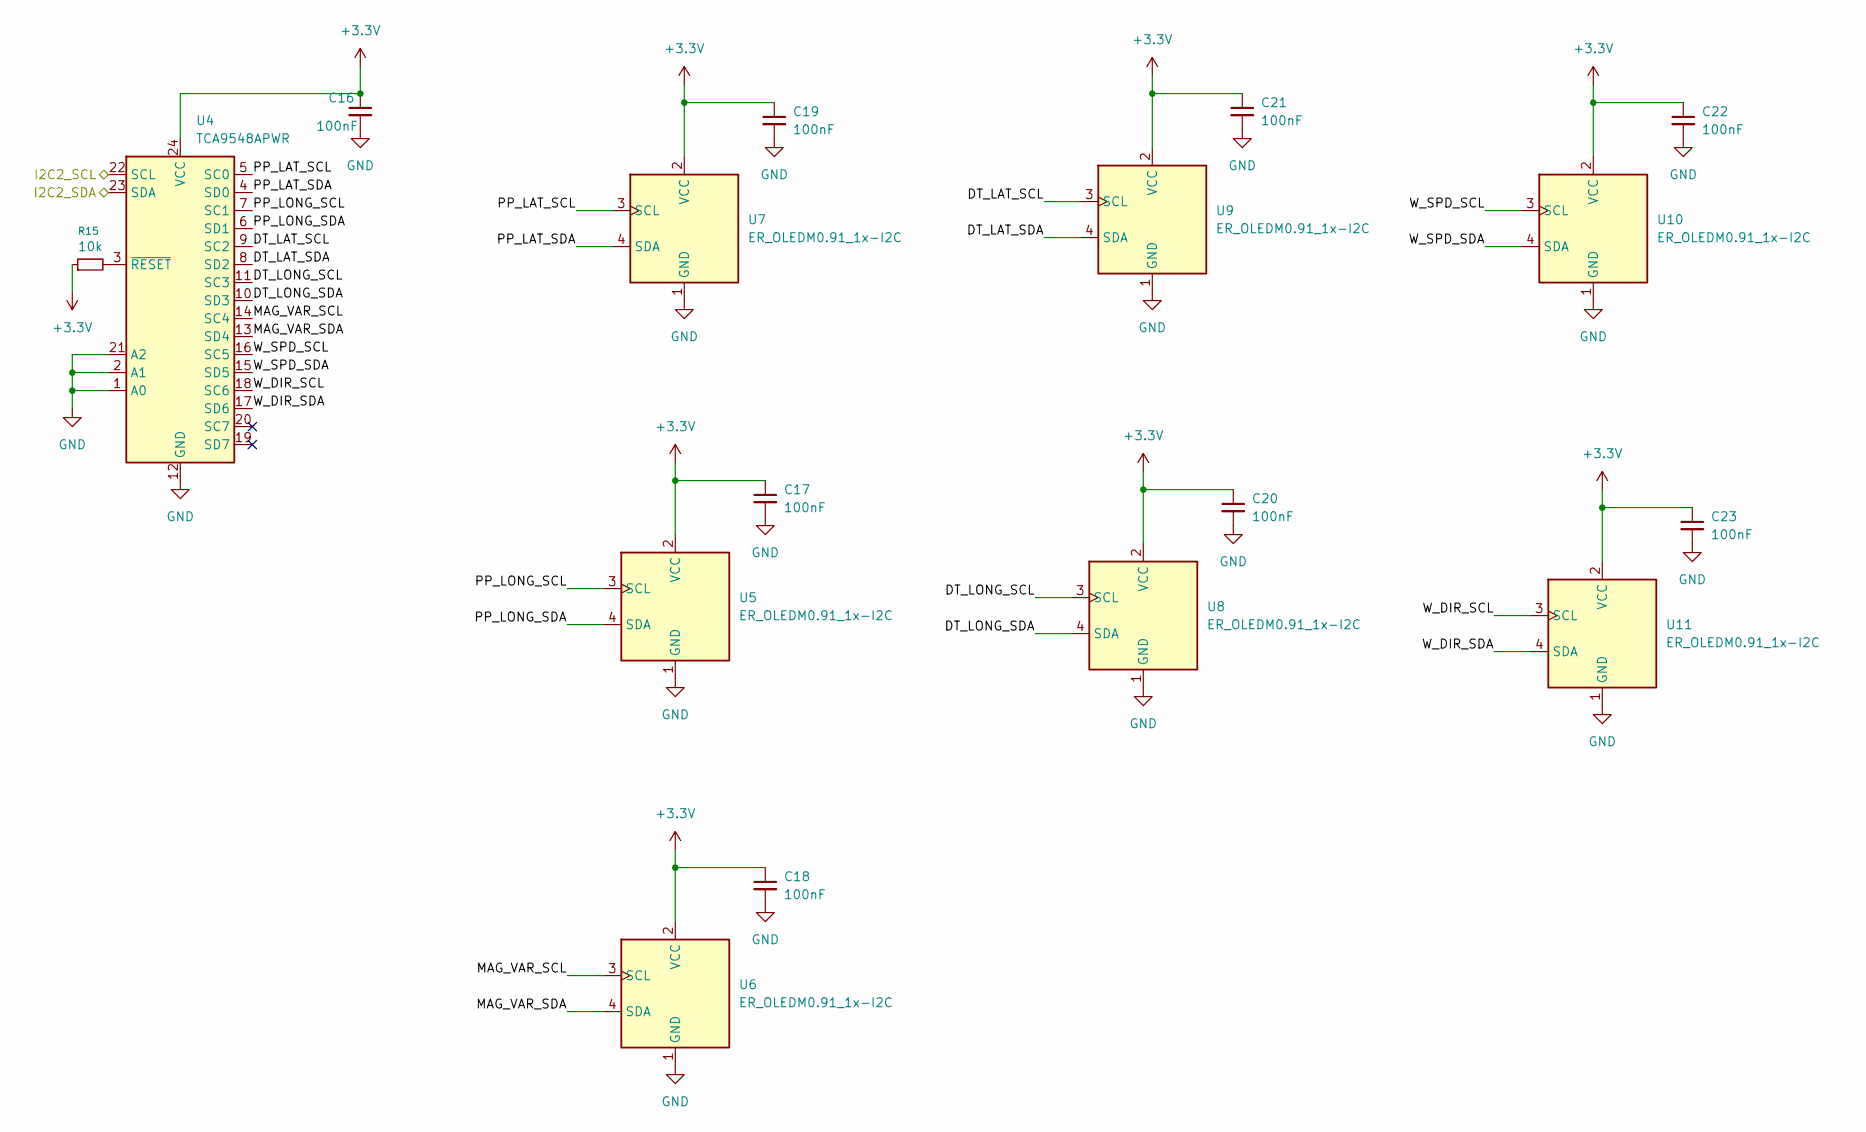
[picture p24: schematic Oled_Displays.kicad_sch]

Parts:
C16, C17, C18, C19, C20, C21, C22, C23: 100nF; C_0805_2012Metric; Tolerance 10%; Rating 50V; LCSC C1711
R15: 10k; R_0805_2012Metric; Tolerance 1%; Rating 1/8W; LCSC C844937
U4: TCA9548APWR; TSSOP-24_4.4x7.8mm_P0.65mm; LCSC C130026
U5, U6, U7, U8, U9, U10, U11: ER_OLEDM0.91_1x-I2C

Connections:
+3.3V: C16.1, C17.1, C18.1, C19.1, C20.1, C21.1, C22.1, C23.1, R15.1, U4.24 (VCC), U5.2 (VCC), U6.2 (VCC), U7.2 (VCC), U8.2 (VCC), U9.2 (VCC), U10.2 (VCC), U11.2 (VCC)
DT_LAT_SCL: U4.9 (SC2), U9.3 (SCL)
DT_LAT_SDA: U4.8 (SD2), U9.4 (SDA)
DT_LONG_SCL: U4.11 (SC3), U8.3 (SCL)
DT_LONG_SDA: U4.10 (SD3), U8.4 (SDA)
GND: C16.2, C17.2, C18.2, C19.2, C20.2, C21.2, C22.2, C23.2, U4.1 (A0), U4.2 (A1), U4.12 (GND), U4.21 (A2), U5.1 (GND), U6.1 (GND), U7.1 (GND), U8.1 (GND), U9.1 (GND), U10.1 (GND), U11.1 (GND)
I2C2_SCL: U4.22 (SCL)
I2C2_SDA: U4.23 (SDA)
MAG_VAR_SCL: U4.14 (SC4), U6.3 (SCL)
MAG_VAR_SDA: U4.13 (SD4), U6.4 (SDA)
unnamed: R15.2, U4.3 (~RESET)
PP_LAT_SCL: U4.5 (SC0), U7.3 (SCL)
PP_LAT_SDA: U4.4 (SD0), U7.4 (SDA)
PP_LONG_SCL: U4.7 (SC1), U5.3 (SCL)
PP_LONG_SDA: U4.6 (SD1), U5.4 (SDA)
W_DIR_SCL: U4.18 (SC6), U11.3 (SCL)
W_DIR_SDA: U4.17 (SD6), U11.4 (SDA)
W_SPD_SCL: U4.16 (SC5), U10.3 (SCL)
W_SPD_SDA: U4.15 (SD5), U10.4 (SDA)
