OpenSkyHawk/OpenSkyhawk/PCB/Right_Console/Right_Navigation/ASN-41_NavComputer/Switches.kicad_sch

## KiCad design PCB/Right_Console/Right_Navigation/ASN-41_NavComputer/Switches.kicad_sch (2026-07-10)

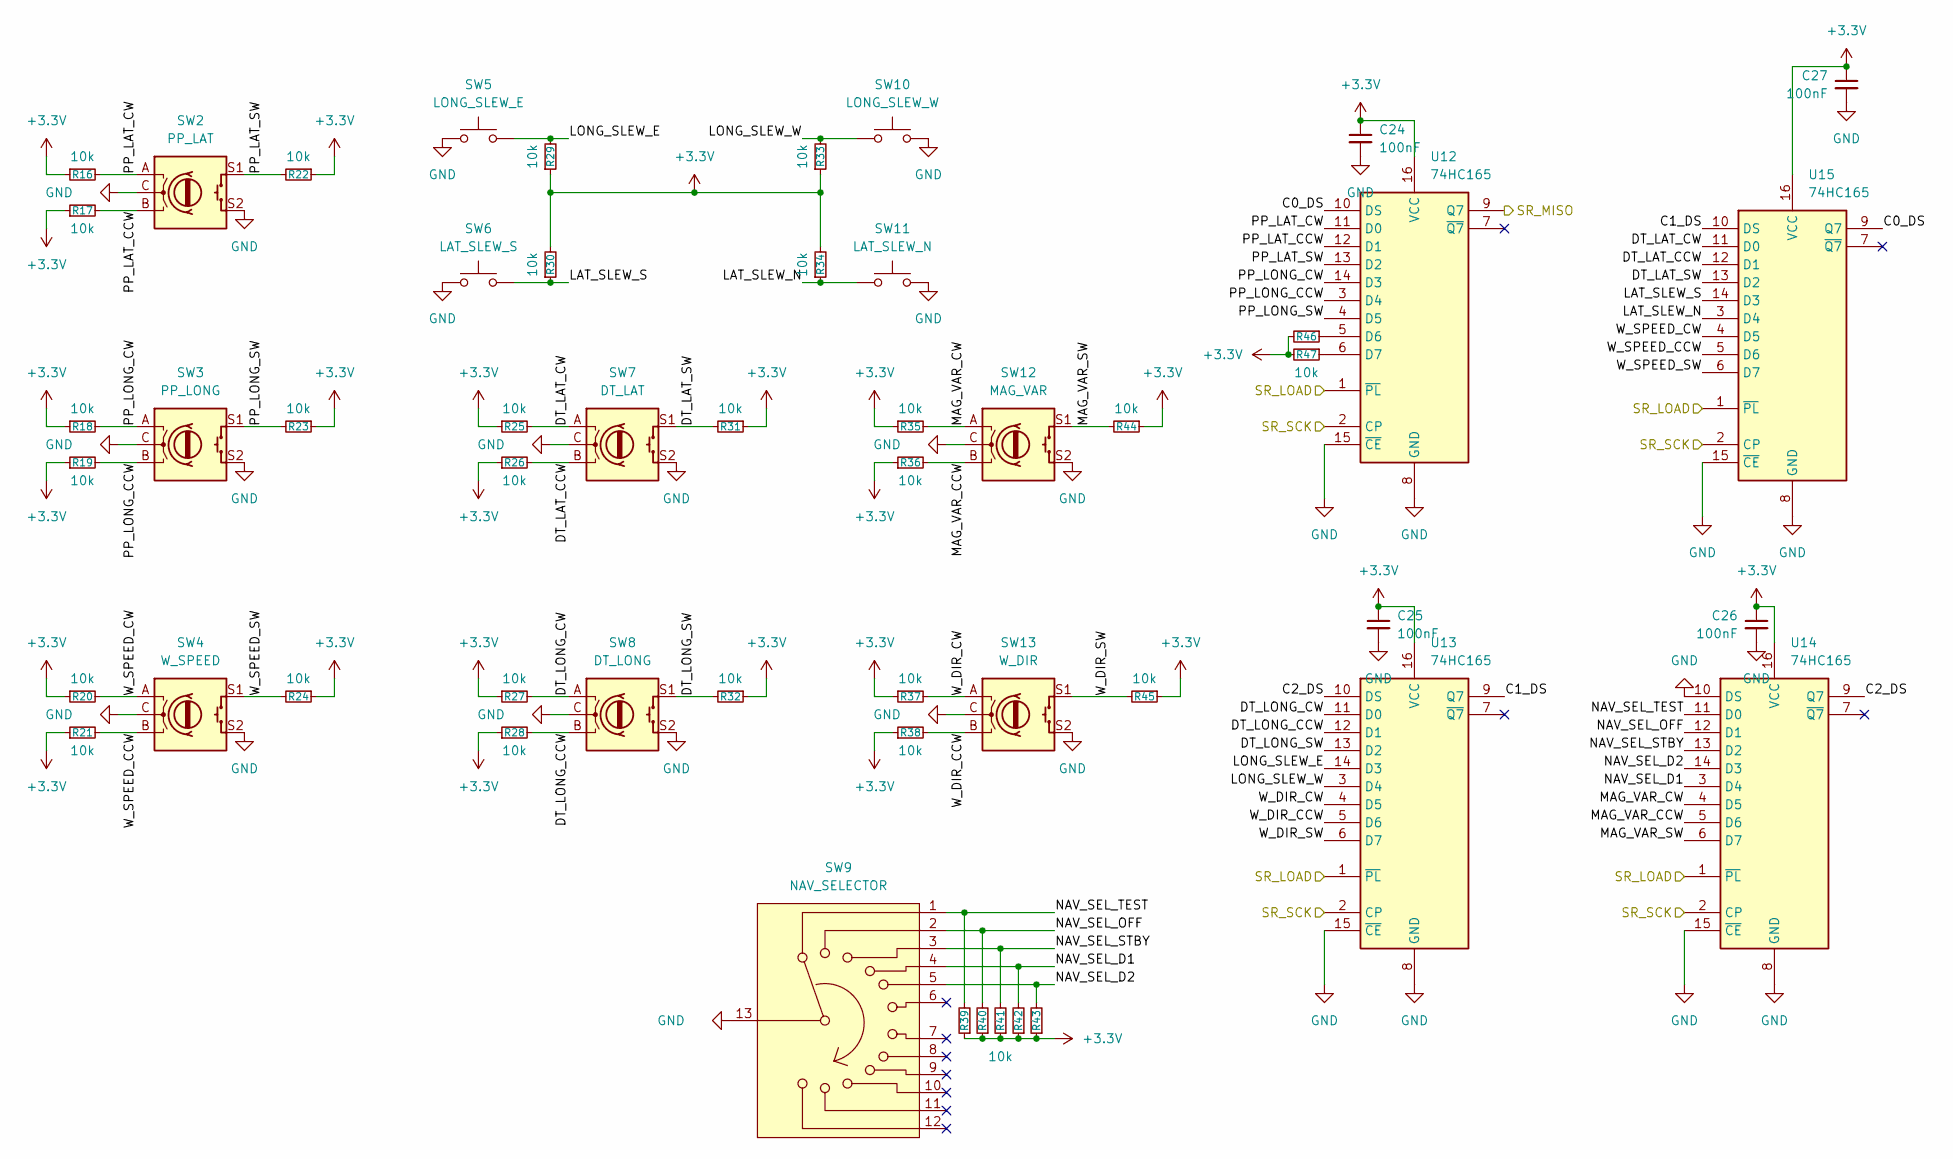
[picture p25: schematic Switches.kicad_sch]

Parts:
C24, C25, C26, C27: 100nF; C_0805_2012Metric; Tolerance 10%; Rating 50V; LCSC C1711
R16, R17, R18, R19, R20, R21, R22, R23, R24, R25, R26, R27, R28, R29, R30, R31, R32, R33, R34, R35, R36, R37, R38, R39, R40, R41, R42, R43, R44, R45, R46, R47: 10k; R_0805_2012Metric; Tolerance 1%; Rating 1/8W; LCSC C844937
SW2: PP_LAT
SW3: PP_LONG
SW4: W_SPEED
SW5: LONG_SLEW_E
SW6: LAT_SLEW_S
SW7: DT_LAT
SW8: DT_LONG
SW9: NAV_SELECTOR
SW10: LONG_SLEW_W
SW11: LAT_SLEW_N
SW12: MAG_VAR
SW13: W_DIR
U12, U13, U14, U15: 74HC165; SOIC-16_3.9x9.9mm_P1.27mm; LCSC C22384789

Connections:
+3.3V: C24.1, C25.1, C26.1, C27.1, R16.1, R17.1, R18.1, R19.1, R20.1, R21.1, R22.1, R23.1, R24.1, R25.1, R26.1, R27.1, R28.1, R29.1, R30.2, R31.1, R32.1, R33.1, R34.2, R35.1, R36.1, R37.1, R38.1, R39.1, R40.1, R41.1, R42.1, R43.1, R44.1, R45.1, R46.2, R47.2, U12.16 (VCC), U13.16 (VCC), U14.16 (VCC), U15.16 (VCC)
C0_DS: U12.10 (DS), U15.9 (Q7)
C1_DS: U13.9 (Q7), U15.10 (DS)
C2_DS: U13.10 (DS), U14.9 (Q7)
DT_LAT_CCW: R26.2, SW7.B, U15.12 (D1)
DT_LAT_CW: R25.2, SW7.A, U15.11 (D0)
DT_LAT_SW: R31.2, SW7.S1, U15.13 (D2)
DT_LONG_CCW: R28.2, SW8.B, U13.12 (D1)
DT_LONG_CW: R27.2, SW8.A, U13.11 (D0)
DT_LONG_SW: R32.2, SW8.S1, U13.13 (D2)
GND: C24.2, C25.2, C26.2, C27.2, SW2.C, SW2.S2, SW3.C, SW3.S2, SW4.C, SW4.S2, SW5.1, SW6.1, SW7.C, SW7.S2, SW8.C, SW8.S2, SW9.13, SW10.2, SW11.2, SW12.C, SW12.S2, SW13.C, SW13.S2, U12.8 (GND), U12.15 (~CE), U13.8 (GND), U13.15 (~CE), U14.8 (GND), U14.10 (DS), U14.15 (~CE), U15.8 (GND), U15.15 (~CE)
LAT_SLEW_N: R34.1, SW11.1, U15.3 (D4)
LAT_SLEW_S: R30.1, SW6.2, U15.14 (D3)
LONG_SLEW_E: R29.2, SW5.2, U13.14 (D3)
LONG_SLEW_W: R33.2, SW10.1, U13.3 (D4)
MAG_VAR_CCW: R36.2, SW12.B, U14.5 (D6)
MAG_VAR_CW: R35.2, SW12.A, U14.4 (D5)
MAG_VAR_SW: R44.2, SW12.S1, U14.6 (D7)
NAV_SEL_D1: R42.2, SW9.4, U14.3 (D4)
NAV_SEL_D2: R43.2, SW9.5, U14.14 (D3)
NAV_SEL_OFF: R40.2, SW9.2, U14.12 (D1)
NAV_SEL_STBY: R41.2, SW9.3, U14.13 (D2)
NAV_SEL_TEST: R39.2, SW9.1, U14.11 (D0)
unnamed: R46.1, U12.5 (D6)
unnamed: R47.1, U12.6 (D7)
PP_LAT_CCW: R17.2, SW2.B, U12.12 (D1)
PP_LAT_CW: R16.2, SW2.A, U12.11 (D0)
PP_LAT_SW: R22.2, SW2.S1, U12.13 (D2)
PP_LONG_CCW: R19.2, SW3.B, U12.3 (D4)
PP_LONG_CW: R18.2, SW3.A, U12.14 (D3)
PP_LONG_SW: R23.2, SW3.S1, U12.4 (D5)
SR_LOAD: U12.1 (~PL), U13.1 (~PL), U14.1 (~PL), U15.1 (~PL)
SR_MISO: U12.9 (Q7)
SR_SCK: U12.2 (CP), U13.2 (CP), U14.2 (CP), U15.2 (CP)
W_DIR_CCW: R38.2, SW13.B, U13.5 (D6)
W_DIR_CW: R37.2, SW13.A, U13.4 (D5)
W_DIR_SW: R45.2, SW13.S1, U13.6 (D7)
W_SPEED_CCW: R21.2, SW4.B, U15.5 (D6)
W_SPEED_CW: R20.2, SW4.A, U15.4 (D5)
W_SPEED_SW: R24.2, SW4.S1, U15.6 (D7)
