OpenSkyHawk/OpenSkyhawk/Firmware/Tests/SwitchMultiPos/tests/configure/configure.cpp

// SwitchMultiPos — configure test
//
// configure() must emit nothing; poll() must be a no-op until forceReport() runs once.
// Verified via emitCount(). CAN runs in NORMAL mode — the node ACKs the (unmodified) PanelBridge.
//
// Rig: STM32 on the CAN bus with the PanelBridge. Jumper PB0->PA0, PB1->PA1, PB4->PA4, PB5->PA5.

#include <Arduino.h>
#include <STM32Board.h>
#include <Inputs/SwitchMultiPos/SwitchMultiPos.h>

static constexpr uint16_t CTRL_ID = 0x5678;
static constexpr uint8_t  N       = 4;
static const uint8_t SW_PINS[N]   = { PA0, PA1, PA4, PA5 };
static const uint8_t CTRL_PINS[N] = { PB0, PB1, PB4, PB5 };

static void setActive(uint8_t idx) {
    for (uint8_t i = 0; i < N; i++) digitalWrite(CTRL_PINS[i], i == idx ? LOW : HIGH);
    delayMicroseconds(100);
}
static void txPush() { CANProtocol::flushBatched(canIdEvt(NODE_ID)); }   // push EVTs to the bridge

static const PinRef gPins[N] = { PinRef(SW_PINS[0]), PinRef(SW_PINS[1]), PinRef(SW_PINS[2]), PinRef(SW_PINS[3]) };
OpenSkyhawk::SwitchMultiPos gSel(CTRL_ID, gPins, N);

void setup() {
    STM32Board::setDebug(true);
    STM32Board::begin();
    STM32Board::diagSerial().println("=== SwitchMultiPos configure ===");

    bool pass = true;
    auto check = [&](const char* label, bool ok) {
        if (!ok) pass = false;
        STM32Board::diagSerial().print(label);
        STM32Board::diagSerial().println(ok ? ": PASS" : ": FAIL");
    };

    for (uint8_t i = 0; i < N; i++) pinMode(CTRL_PINS[i], OUTPUT);
    setActive(0);
    gSel.configure();
    CANProtocol::start();

    check("configure() emits no EVT", gSel.emitCount() == 0);

    gSel.poll();
    check("poll() before forceReport() is a no-op", gSel.emitCount() == 0);

    gSel.forceReport();
    txPush();
    check("forceReport() then emits once (index 0)", gSel.emitCount() == 1 && gSel.position() == 0);

    STM32Board::diagSerial().println(pass ? "=== ALL PASS ===" : "=== FAIL ===");
}

void loop() {}
