OpenSkyHawk/OpenSkyhawk/Firmware/Tests/DrumDisplay/tests/grouped_decimal/grouped_decimal.cpp

// DrumDisplay — altimeter Kollsman setting (grouped 2+1+1 digits + decimal glyph) test.
//
// SH1106 1.3" @ 0x3C, STM32F103C8. Exercises a multi-digit source (NN00 carries 2 digits) and a
// static '.' glyph cell. Tier A (logic): the 2-digit splice + single-digit splices land "2992";
// the glyph adds a non-rolling cell. Tier B (bench): reads "29.92" with the dot fixed.

#include <Arduino.h>
#include <Wire.h>
#include <math.h>
#include <STM32Board.h>
#include <DrumDisplay.h>
#include <A4EC_OutputIds.h>

using namespace OpenSkyhawk;

U8G2_SH1106_128X64_NONAME_F_HW_I2C oled(U8G2_R0, U8X8_PIN_NONE);

// Readout descriptor — defined in the sketch (panel wiring, like the PinRef map), not a global.
// NN00 carries the top two digits (places 3,2); 00N0 the tens; 000N the ones. '.' after digit 2.
//
// The inHg group is NOT a drum digit pair. avionics.lua sets ALT_ADJ_NNxx to math.floor(alt_setting)
// and mainpanel_init declares that gauge as input {29,30} → output {0,1}, so the export is 0 for 29
// and full scale for 30: two positions offset by 29. The two decimals are ordinary digit drums
// ({0,10} → {0,1}, i.e. digit/10).
static const DrumSource ALT_ADJ_SRC[] = {
    { A_4E_C_ALT_ADJ_NN00, A_4E_C_ALT_ADJ_NN00_AM, 2, 2, /*steps*/ 2, /*mul*/ 1, /*offset*/ 29 },
    { A_4E_C_ALT_ADJ_00N0, A_4E_C_ALT_ADJ_00N0_AM, 1, 1 },
    { A_4E_C_ALT_ADJ_000N, A_4E_C_ALT_ADJ_000N_AM, 1, 0 },
};
static const DrumGlyph ALT_ADJ_DOT[] = {
    { '.', 2, 1.8f },
};
static const DrumReadout ALT_ADJ = {
    .sources = ALT_ADJ_SRC, .nSources = 3, .nDigits = 4,
    .digitWidthMm = 4.5f, .digitHeightMm = 8.0f, .interDigitGapMm = 1.0f,
    .glyphs = ALT_ADJ_DOT, .nGlyphs = 1,
};

DrumDisplay alt(oled, ALT_ADJ, DrumFont::LARGE);

static bool pass = true;
static void check(const char* label, bool ok) {
    if (!ok) pass = false;
    auto& d = STM32Board::diagSerial();
    d.print(ok ? F("[PASS] ") : F("[FAIL] "));
    d.println(label);
}
// One digit 0..9 in a whole word.
static uint16_t digitWord(int digit) {
    // DCS exports a drum digit as digit/10 of the gauge's arg range (utils.lua jumpwheel()
    // returns B/10), and TRUNCATES on the way out — a 9 arrives as 58981, not 65535.
    return static_cast<uint16_t>(digit / 10.0f * 65535.0f);
}
// The inHg group: 29 is the bottom of the declared {29,30} range, 30 the top.
static uint16_t inHgWord(int v) {
    return v >= 30 ? 65535 : 0;
}

void setup() {
    STM32Board::setDebug(true);
    STM32Board::begin();
    auto& d = STM32Board::diagSerial();
    d.println(F("=== DrumDisplay grouped_decimal (ALT_ADJ) ==="));

    Wire.setSCL(I2C_TEST_SCL);
    Wire.setSDA(I2C_TEST_SDA);
    Wire.begin();
    oled.setI2CAddress(0x3C << 1);
    oled.begin();
    alt.configure();

    // 29.92 -> NN00=29, tens=9, ones=2  -> combined 2992.
    alt.onControlPacket(A_4E_C_ALT_ADJ_NN00, inHgWord(29));
    alt.onControlPacket(A_4E_C_ALT_ADJ_00N0, digitWord(9));
    alt.onControlPacket(A_4E_C_ALT_ADJ_000N, digitWord(2));

    check("2-digit splice reconstructs 2992", alt.debugTarget() == 2992);

    // The top of the inHg range must land on 30, not on a scaled-down 29.
    alt.onControlPacket(A_4E_C_ALT_ADJ_NN00, inHgWord(30));
    check("inHg group reaches 30.92        ", alt.debugTarget() == 3092);
    alt.onControlPacket(A_4E_C_ALT_ADJ_NN00, inHgWord(29));
    check("5 visual cells (4 digits + '.' glyph)", alt.debugCellCount() == 5);
    check("row fits <= 128 px", alt.debugRowWidth() <= 128);

    d.println(pass ? F("=== ALL PASS ===") : F("=== FAIL ==="));
}

void loop() {
    alt.update();
}
