OpenSkyHawk/OpenSkyhawk/Firmware/Tests/PanelGroup/tests/register_adc/register_adc.cpp

// PanelGroup — registerADC integration test
//
// Verifies:
//   registerADC(adc, addr, wire) stores the instance without crash.
//   setup() calls adc.begin(addr, wire) — verified by subsequent PinRef readAnalog() working.
//   Registering the same ADS1115 instance twice is deduplicated (no double-begin).
//   A PinRef(adc, channel) reads a valid value after setup() has initialised the chip.
//
// Hardware: ADS1115 dev board on I2C1 remap (J_I2C2: PB10=SCL, PB11=SDA), addr 0x48 (ADDR→GND).
//   A0 connected to ~1.65 V mid-rail (10 kΩ + 10 kΩ voltage divider, 3.3 V → GND).
//   No MCP23017 required. CAN loopback used so no physical bus needed.
//
// Note: CAN startup (READY frame) is verified in test_boot_sequence — not checked here.

#include <Arduino.h>
#include <STM32Board.h>
#include <Wire.h>
#include <PanelGroup.h>

static ADS1115 gAdc;

void setup() {
    STM32Board::setDebug(true);
    STM32Board::begin();
    STM32Board::diagSerial().println("=== PanelGroup register_adc ===");
    STM32Board::diagSerial().println("Hardware: ADS1115 @ 0x48, A0 at ~1.65 V mid-rail");

    bool pass = true;
    auto check = [&](const char* label, bool cond) {
        if (!cond) pass = false;
        STM32Board::diagSerial().print(label);
        STM32Board::diagSerial().println(cond ? ": PASS" : ": FAIL");
    };

    // Register ADC before setup() — pattern identical to sketch usage
    Wire.setSDA(I2C_TEST_SDA);
    Wire.setSCL(I2C_TEST_SCL);
    Wire.begin(); // Bench workaround: production PCB uses Wire.begin() default (PB6/PB7).
    PanelGroup::registerADC(gAdc, 0x48, Wire);

    // Register same instance again — must be deduplicated (no crash, no double-init)
    PanelGroup::registerADC(gAdc, 0x48, Wire);
    STM32Board::diagSerial().println("Double-register: did not crash");

    // Start CAN in loopback so setup() does not hang waiting for bus
    CANProtocol::startLoopback();

    // setup() calls adc.begin(0x48, &Wire) for every registered ADC
    PanelGroup::setup();

    // After setup(), the ADS1115 is initialised — PinRef can read
    PinRef pin(gAdc, 0); // channel 0 = A0
    uint16_t val = pin.readAnalog();
    STM32Board::diagSerial().print("PinRef(adc, 0).readAnalog() = ");
    STM32Board::diagSerial().println(val);

    check("readAnalog() > 0        (ADS1115 responding)", val > 0);
    check("readAnalog() <= 65534   (15-bit×2 range)",     val <= 65534u);
    check("readAnalog() in [8000, 56000] (mid-rail ~1.65 V)",
          val >= 8000 && val <= 56000);

    STM32Board::diagSerial().println(pass ? "=== ALL PASS ===" : "=== FAIL ===");
}

void loop() {
    PanelGroup::loop();
}
