OpenSkyHawk/OpenSkyhawk/Firmware/Tests/RotaryEncoder/tests/bounce/bounce.cpp

// RotaryEncoder — bounce test
//
// At OpenSkyhawk::EncoderStepsPerDetent::Four, jitter back and forth within a detent (forward 1 / back 1, repeated)
// keeps |delta| below the detent threshold → no spurious EVT. This is the detent-level glitch
// rejection (stepsPerDetent > 1).
//
// Rig: this STM32 alone, CAN in silent loopback (no bus, no PanelBridge, no encoder hardware).
// Do NOT run it on a board wired to a live bus: a loopback node never ACKs, which drives the
// bridge error-passive. PASS/FAIL comes from the encoder's own test seams, not from CAN.

#include <Arduino.h>
#include <STM32Board.h>
#include <Inputs/RotaryEncoder/RotaryEncoder.h>

static constexpr uint16_t CTRL_ID = 0x567B;

OpenSkyhawk::RotaryEncoder gEnc(CTRL_ID, PinRef(PA0), PinRef(PA1), OpenSkyhawk::EncoderStepsPerDetent::Four);

void setup() {
    STM32Board::setDebug(true);
    STM32Board::begin();
    STM32Board::diagSerial().println("=== RotaryEncoder bounce ===");

    bool pass = true;
    auto check = [&](const char* label, bool ok) {
        if (!ok) pass = false;
        STM32Board::diagSerial().print(label);
        STM32Board::diagSerial().println(ok ? ": PASS" : ": FAIL");
    };

    gEnc.configure();
    CANProtocol::startLoopback();

    gEnc.debugSeed(0);
    gEnc.debugStep(1); gEnc.debugStep(0);   // forward 1, back 1
    gEnc.debugStep(1); gEnc.debugStep(0);   // again — delta oscillates 1/0, never reaches 4
    check("jitter within detent: no EVT", gEnc.emitCount() == 0);

    CANProtocol::flushBatched(canIdEvt(NODE_ID));
    STM32Board::diagSerial().println(pass ? "=== ALL PASS ===" : "=== FAIL ===");
}

void loop() {}
